makreck/Rase/images/probe/Type_B/Handheld_measuring_probe_08.png

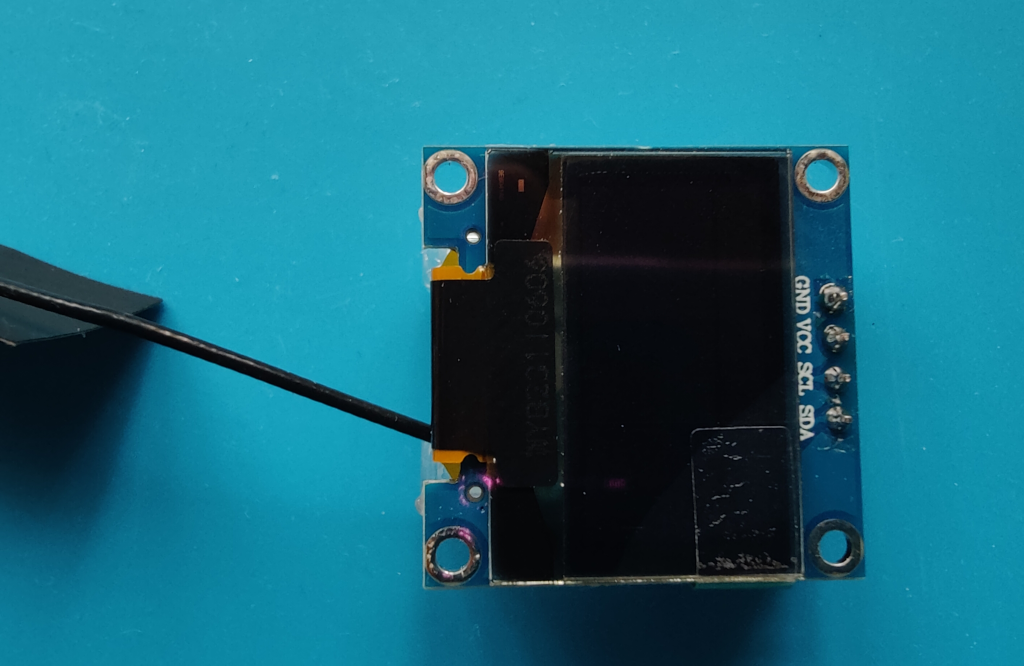
images/probe/Type_B/Handheld_measuring_probe_08.png
