makreck/Rase/images/probe/Type_B/Handheld_measuring_probe_10.png

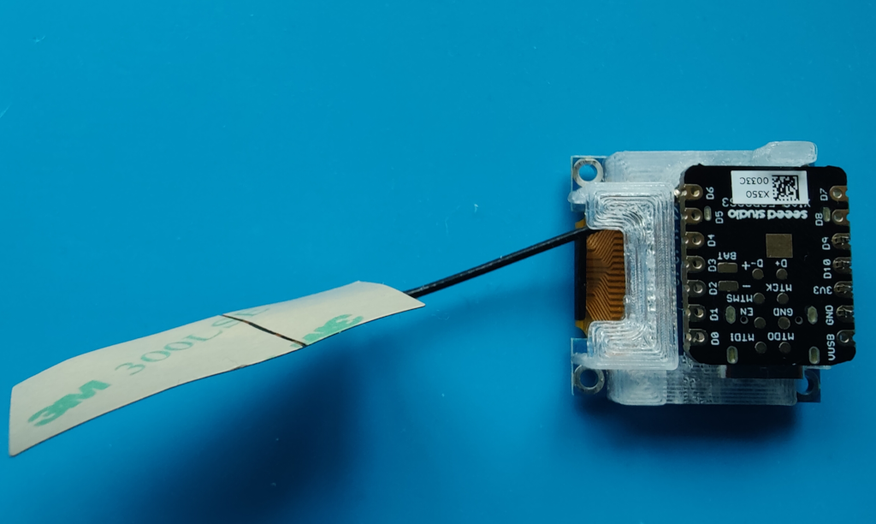
images/probe/Type_B/Handheld_measuring_probe_10.png
