makreck/Rase/images/probe/Type_B/Handheld_measuring_probe_11.png

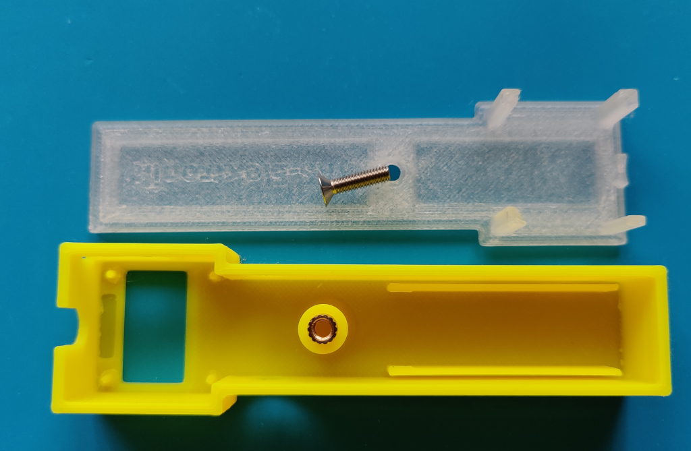
images/probe/Type_B/Handheld_measuring_probe_11.png
