makreck/Rase/images/probe/Type_C/Battless_Rev_C_Menue.jpg

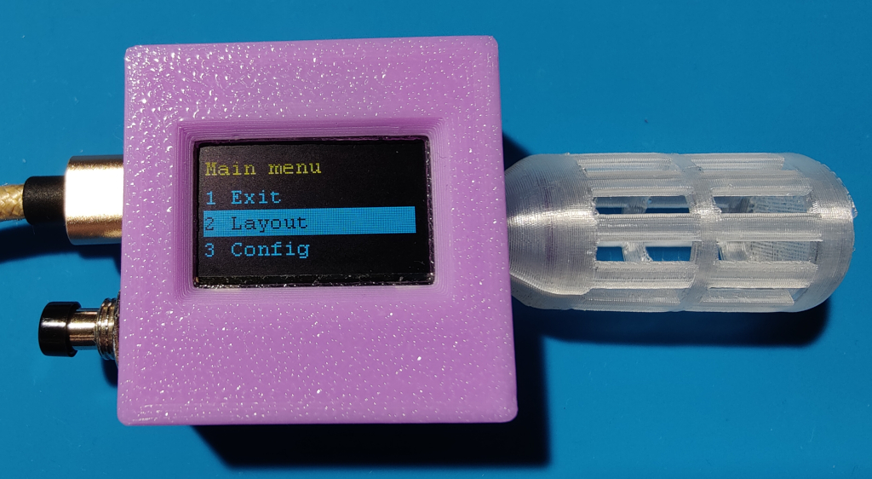
images/probe/Type_C/Battless_Rev_C_Menue.jpg
