makreck/Rase/images/probe/Type_C/Battless_Rev_C_Waveshare_ESP32S3_mini.jpg

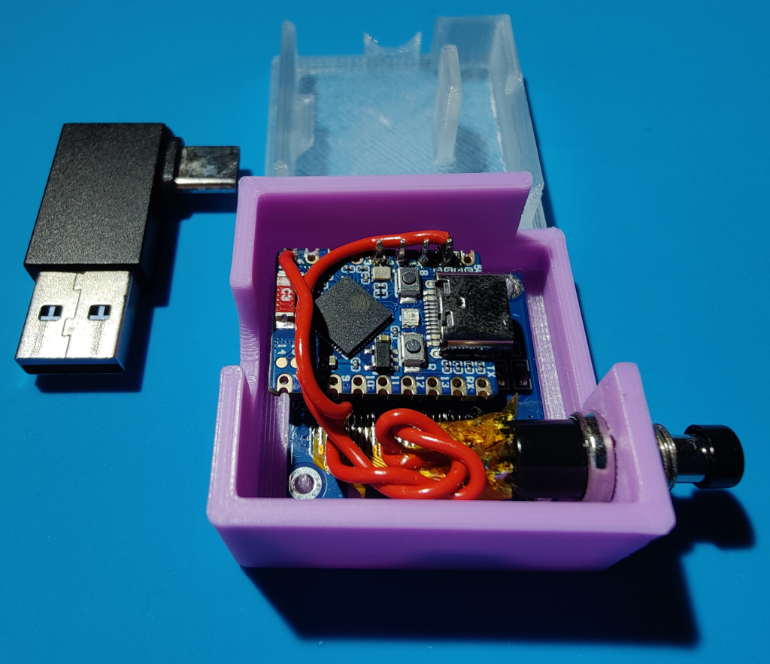
images/probe/Type_C/Battless_Rev_C_Waveshare_ESP32S3_mini.jpg
