makreck/Rase/images/probe/Type_C/Board_Size_ESP32-S3_Super_Mini.jpg

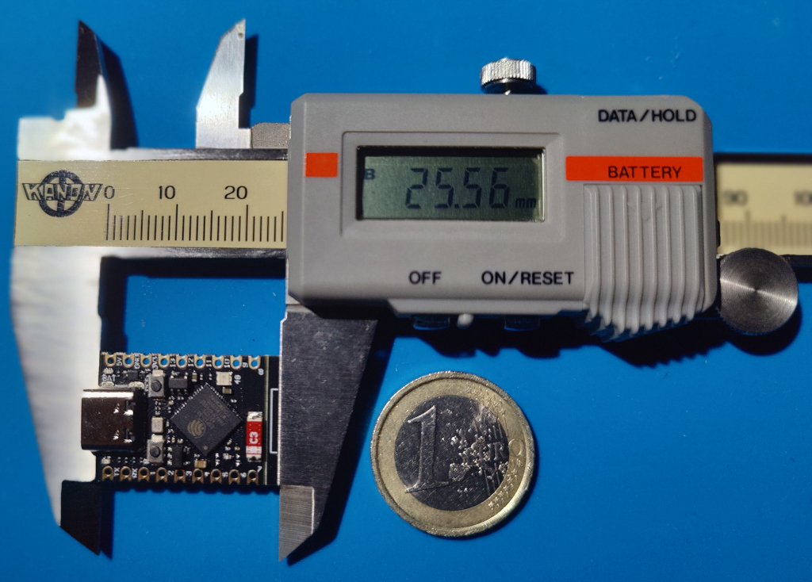
images/probe/Type_C/Board_Size_ESP32-S3_Super_Mini.jpg
