makreck/Rase/images/probe/Type_C/Board_Size_XIAO_ESP32-S3.jpg

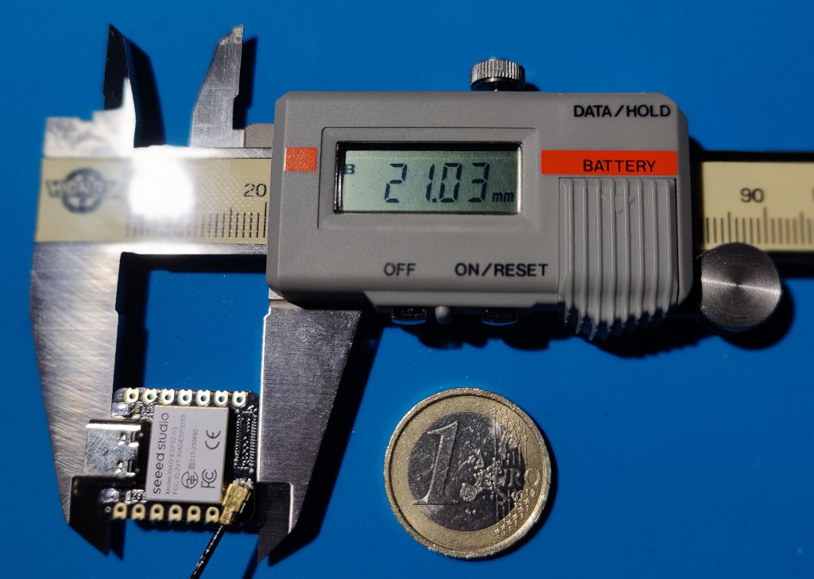
images/probe/Type_C/Board_Size_XIAO_ESP32-S3.jpg
