makreck/Rase/images/probe/Type_C/Board_Type_Sizes.jpg

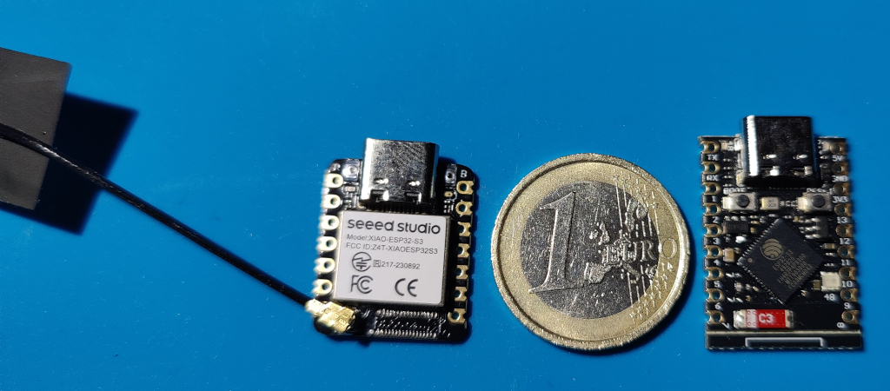
images/probe/Type_C/Board_Type_Sizes.jpg
