makreck/Rase/images/probe/Type_C/Board_Types_Front.jpg

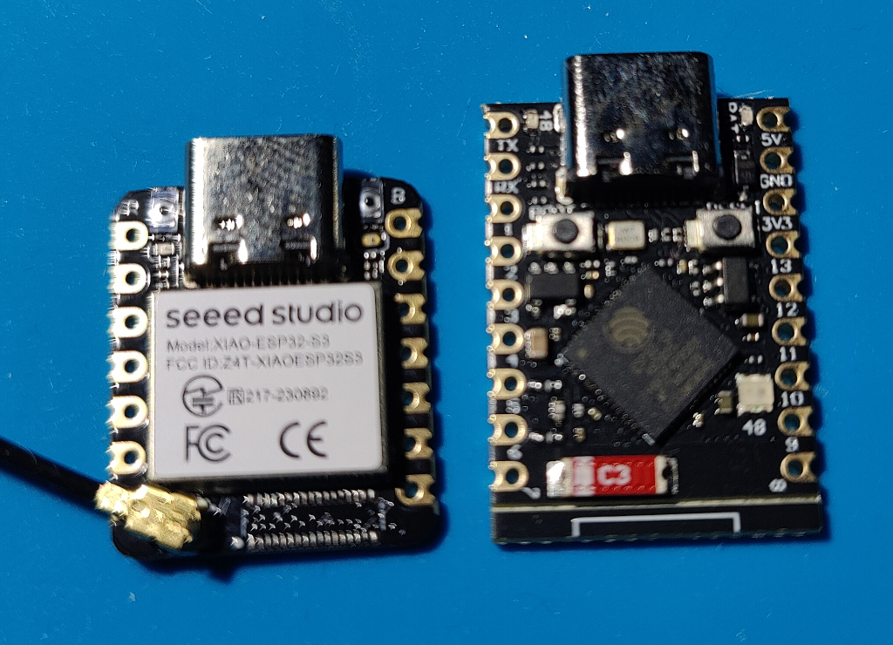
images/probe/Type_C/Board_Types_Front.jpg
