makreck/Rase/images/probe/Type_C/Board_Types_Rear.jpg

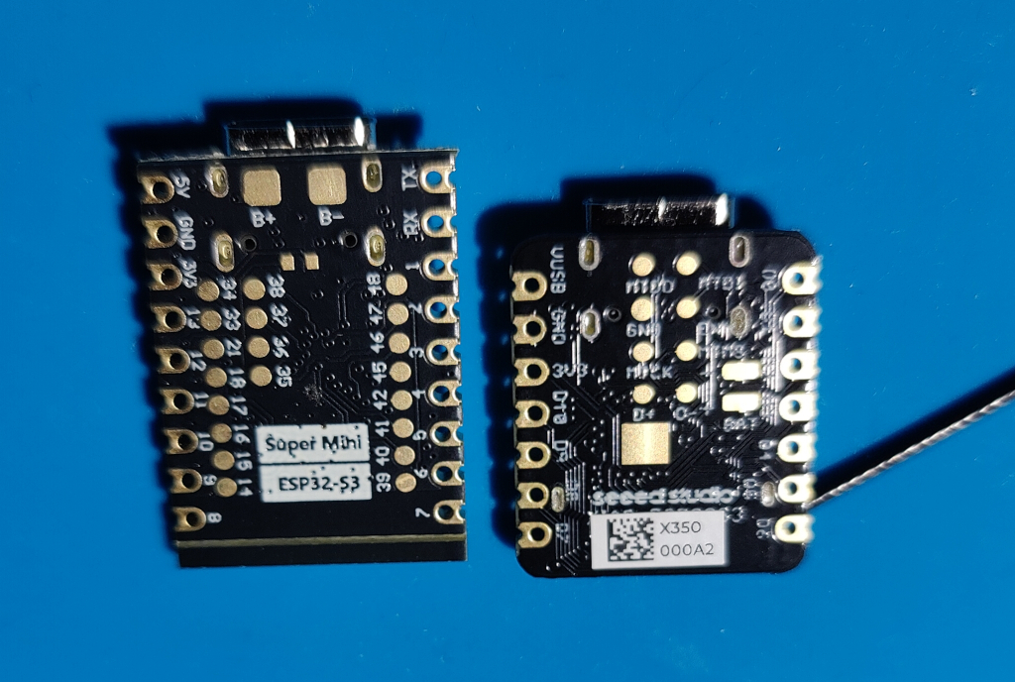
images/probe/Type_C/Board_Types_Rear.jpg
