makreck/Rase/images/probe/Type_C/Housing_Rec_C_M4_Press-Fit-Nut_B.jpg

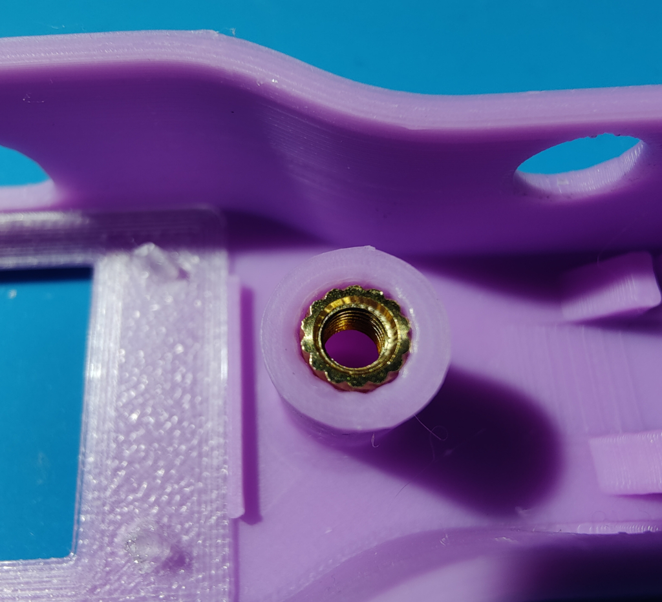
images/probe/Type_C/Housing_Rec_C_M4_Press-Fit-Nut_B.jpg
