makreck/Rase/images/probe/Type_C/Housing_Rec_C_M4_Screw.jpg

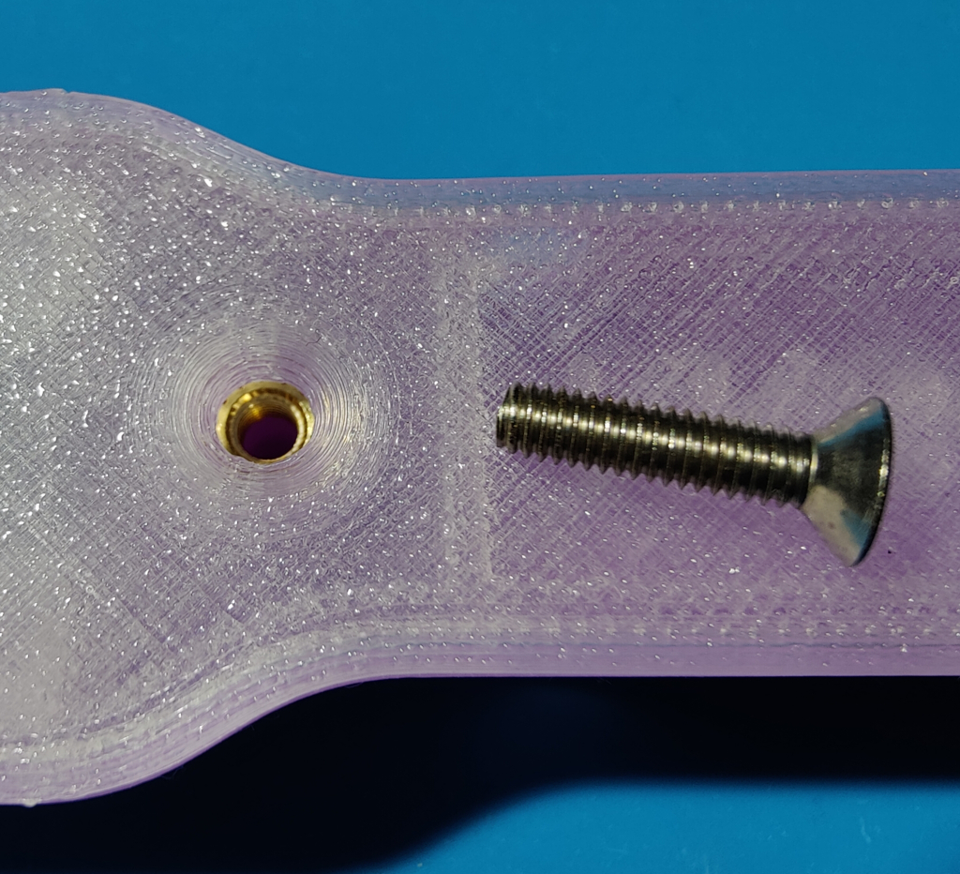
images/probe/Type_C/Housing_Rec_C_M4_Screw.jpg
