makreck/Rase/images/probe/Type_C/Housing_Rec_C_Press-Fit-Nut_A.jpg

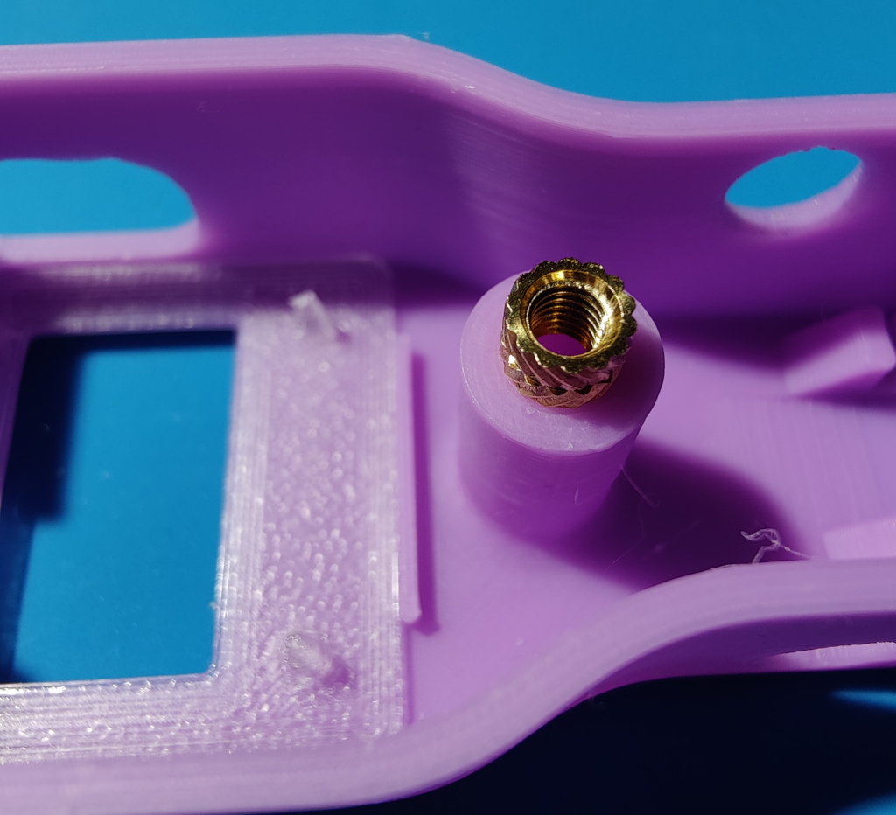
images/probe/Type_C/Housing_Rec_C_Press-Fit-Nut_A.jpg
