makreck/Rase/images/probe/Type_C/Housings_Rev_C.jpg

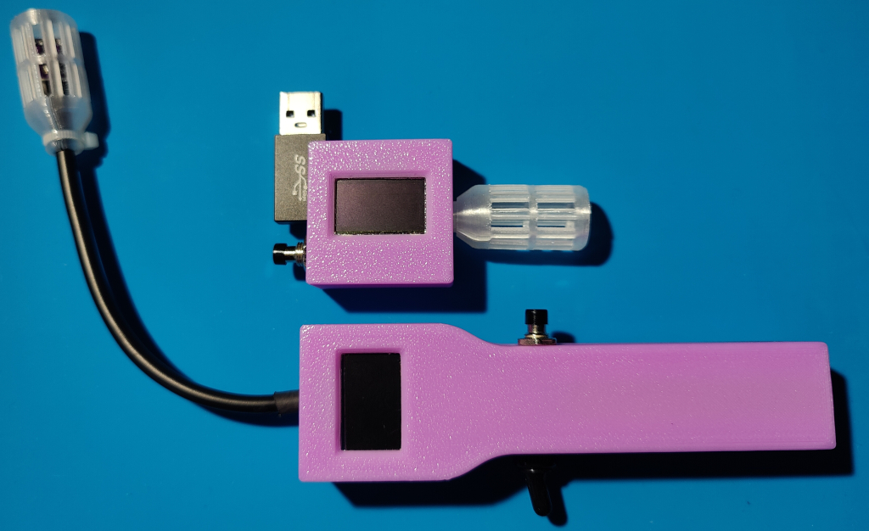
images/probe/Type_C/Housings_Rev_C.jpg
