makreck/Rase/images/probe/Type_C/Insert_Display_Shield.jpg

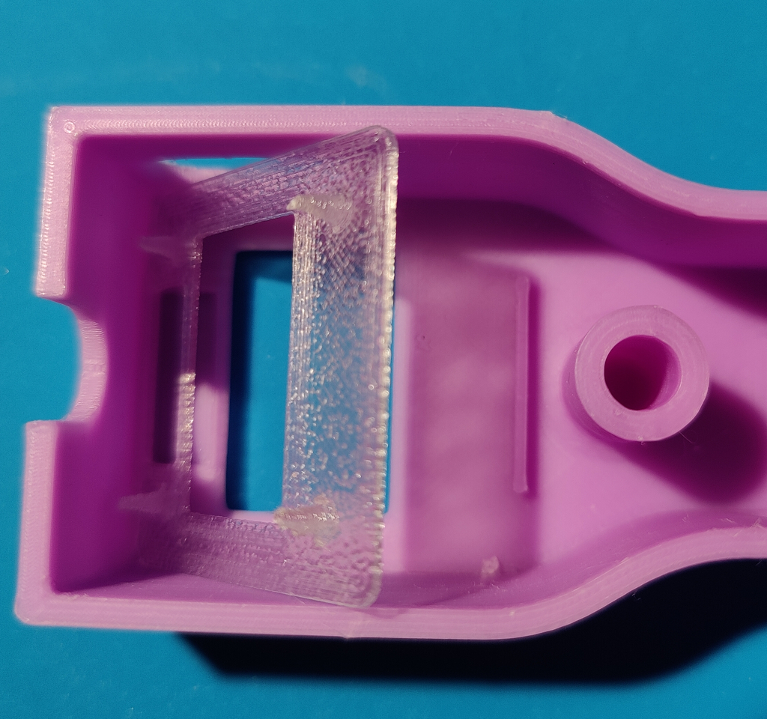
images/probe/Type_C/Insert_Display_Shield.jpg
