makreck/Rase/images/probe/Type_C/Inserted_Display_Shield.jpg

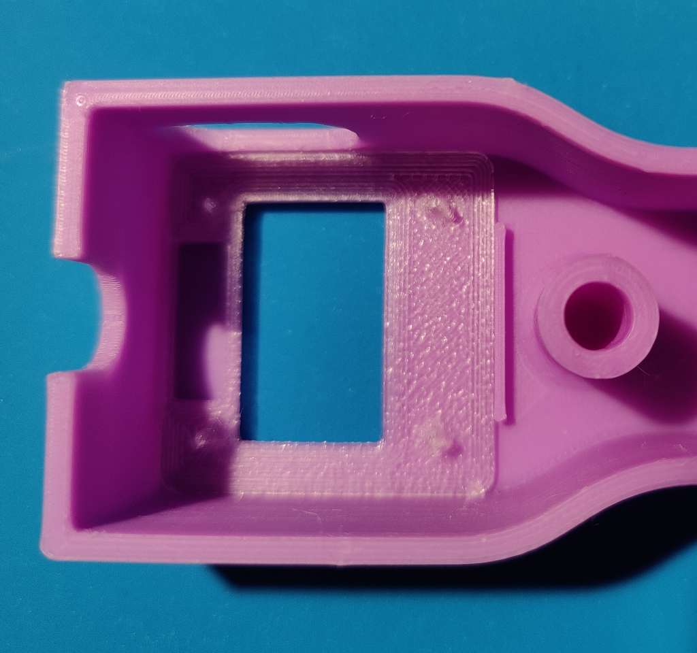
images/probe/Type_C/Inserted_Display_Shield.jpg
