makreck/Rase/images/probe/Type_C/OLED_096_12864_Display_on_Shield.jpg

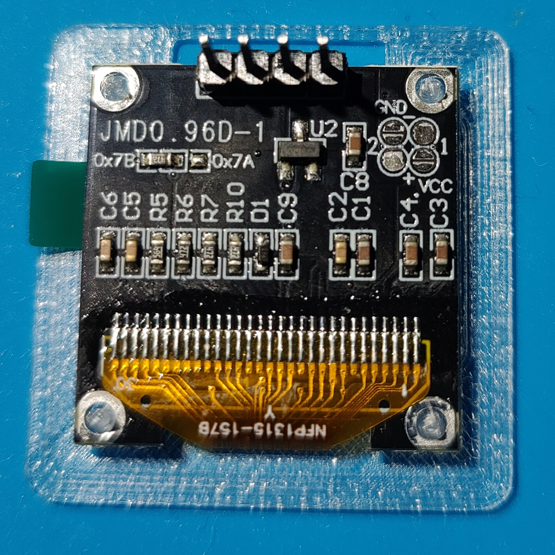
images/probe/Type_C/OLED_096_12864_Display_on_Shield.jpg
