makreck/Rase/images/probe/Type_C/OLED_096_12864_Display_Type_A.jpg

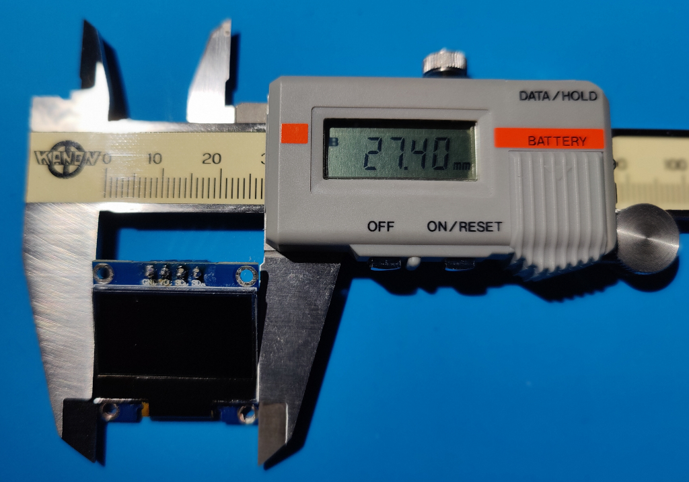
images/probe/Type_C/OLED_096_12864_Display_Type_A.jpg
