makreck/Rase/images/probe/Type_C/OLED_096_12864_Display_Types.jpg

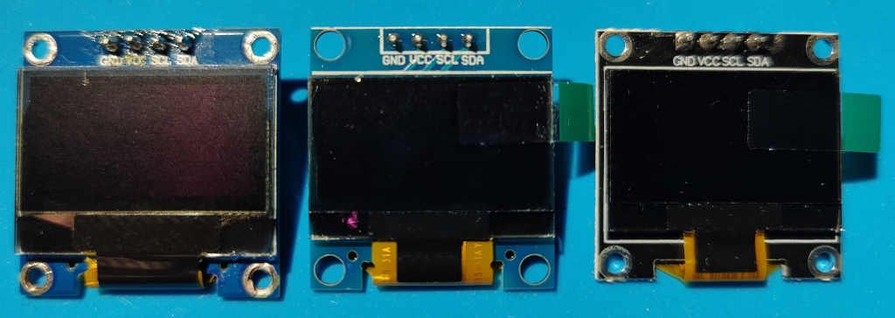
images/probe/Type_C/OLED_096_12864_Display_Types.jpg
