makreck/Rase/images/probe/Type_C/OLED_096_12864_Display_Types_B.jpg

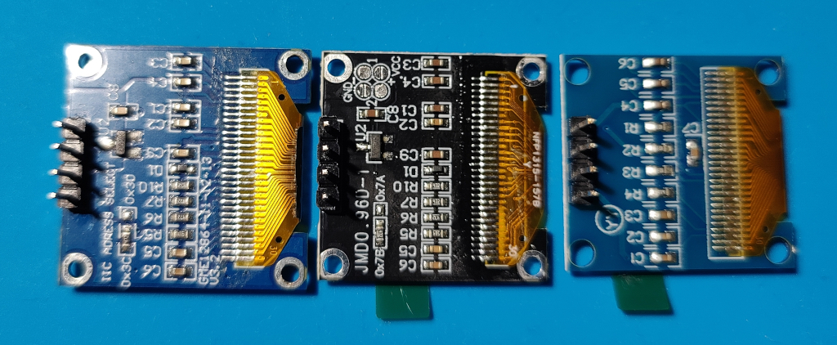
images/probe/Type_C/OLED_096_12864_Display_Types_B.jpg
