makreck/Rase/images/probe/Type_C/Rev_C_complete_open.jpg

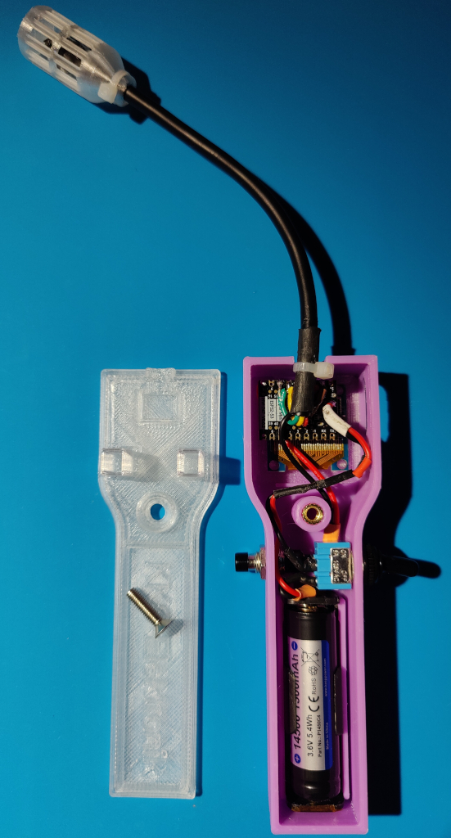
images/probe/Type_C/Rev_C_complete_open.jpg
