makreck/Rase/images/probe/Type_C/Sensor_Protector.jpg

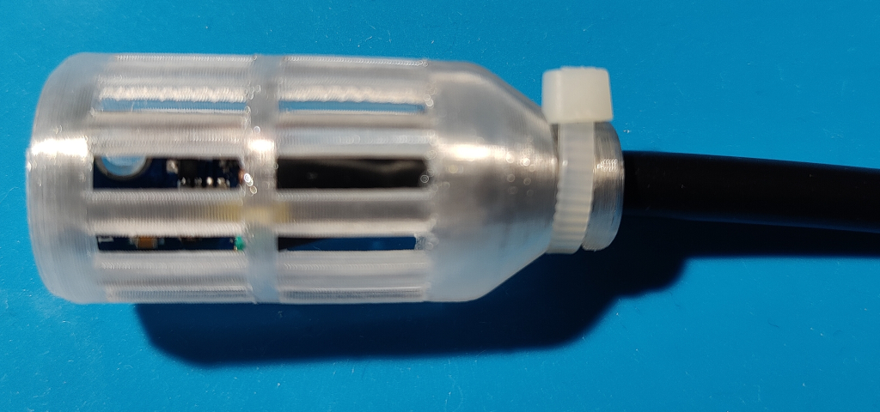
images/probe/Type_C/Sensor_Protector.jpg
