makreck/Rase/images/tool/RASE-Config-Tool.png

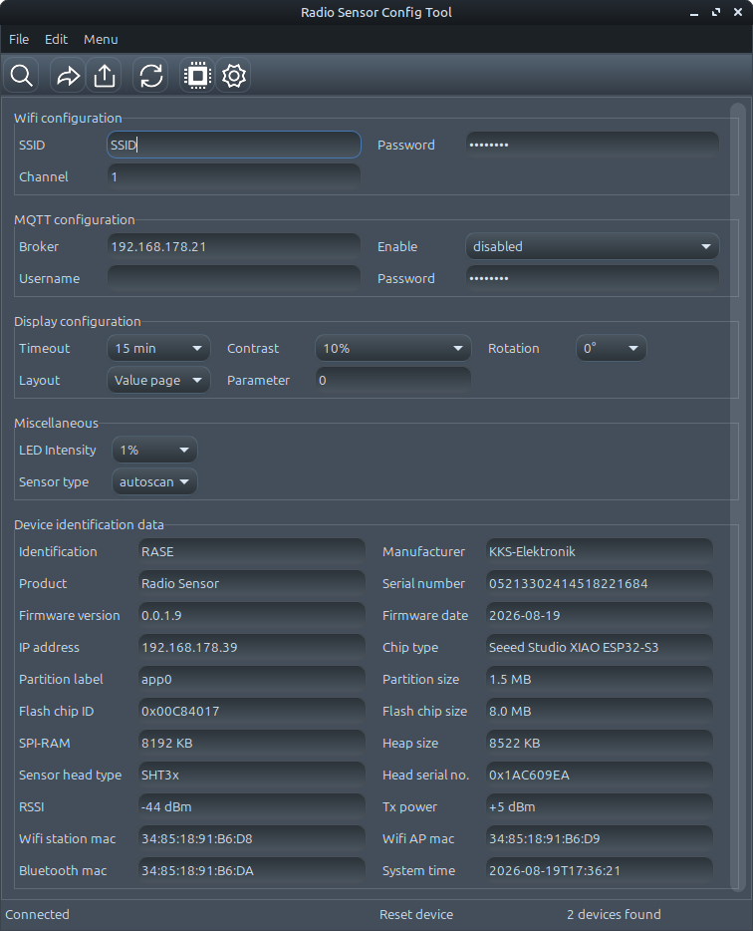
images/tool/RASE-Config-Tool.png
