makreck/Rase/images/web-interface/RASE-Root-Website.png

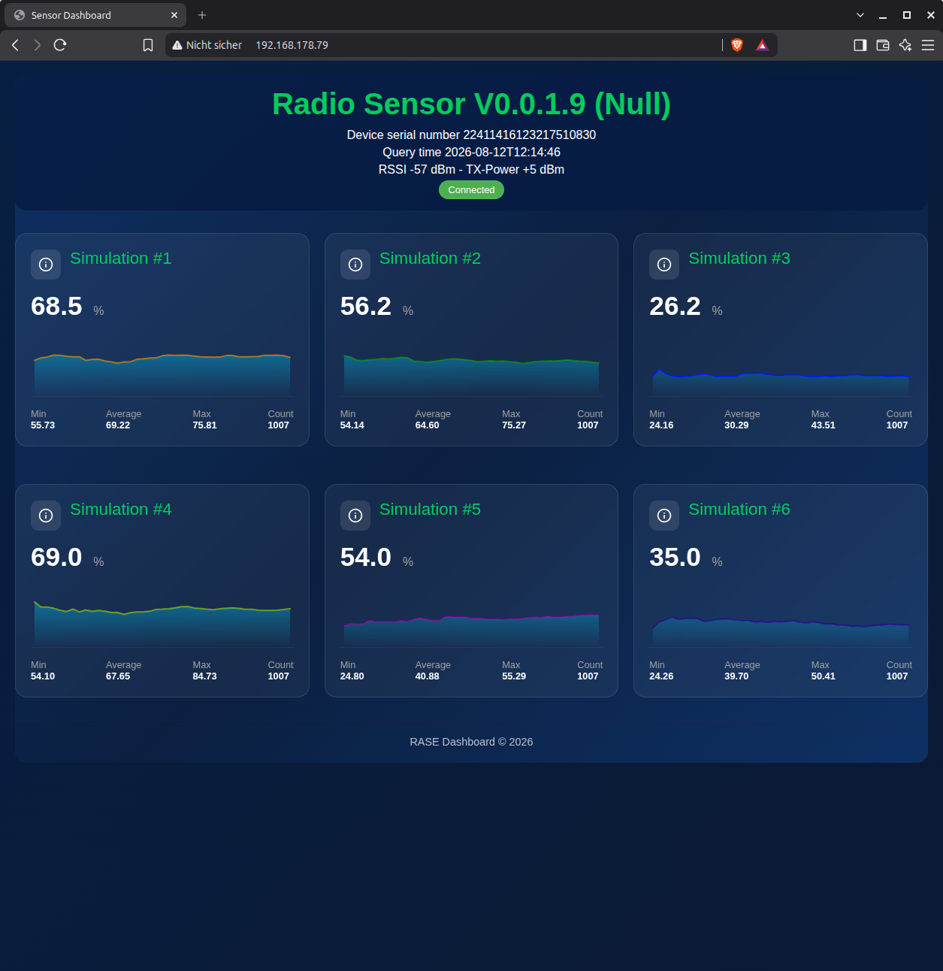
images/web-interface/RASE-Root-Website.png
