makreck/Rase/mechanical/housing/Rev_B/STL/SeeedStudio_XIAO_ESP32S3_Housing_Body.stl

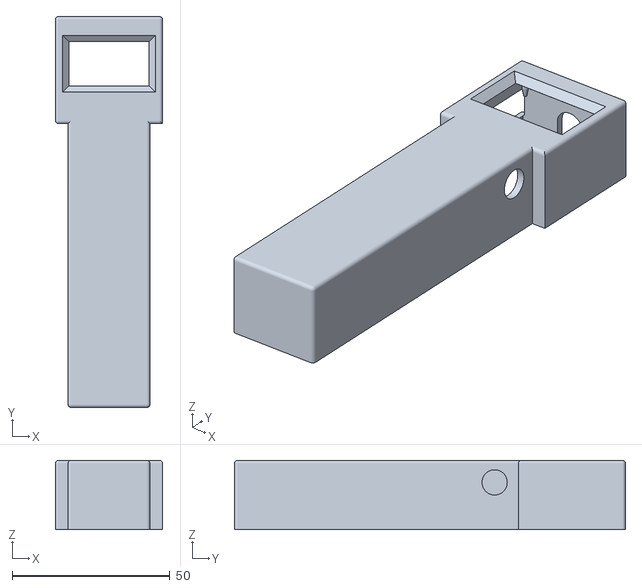
[picture p56: CAD file, 2026-06-11, an earlier design]
mechanical/housing/Rev_B/STL/SeeedStudio_XIAO_ESP32S3_Housing_Body.stl
34.0 x 124.0 x 22.0
