makreck/Rase/images/calibration/Deliquescence_humidity_container_1.png

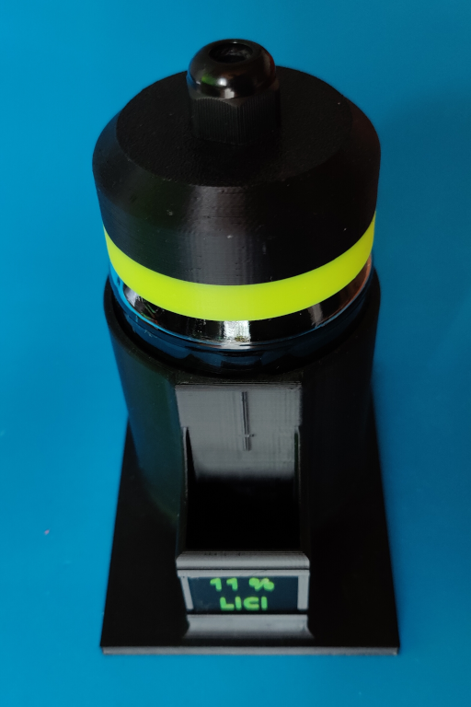
images/calibration/Deliquescence_humidity_container_1.png
