makreck/Rase/images/calibration/Deliquescence_humidity_container_2.png

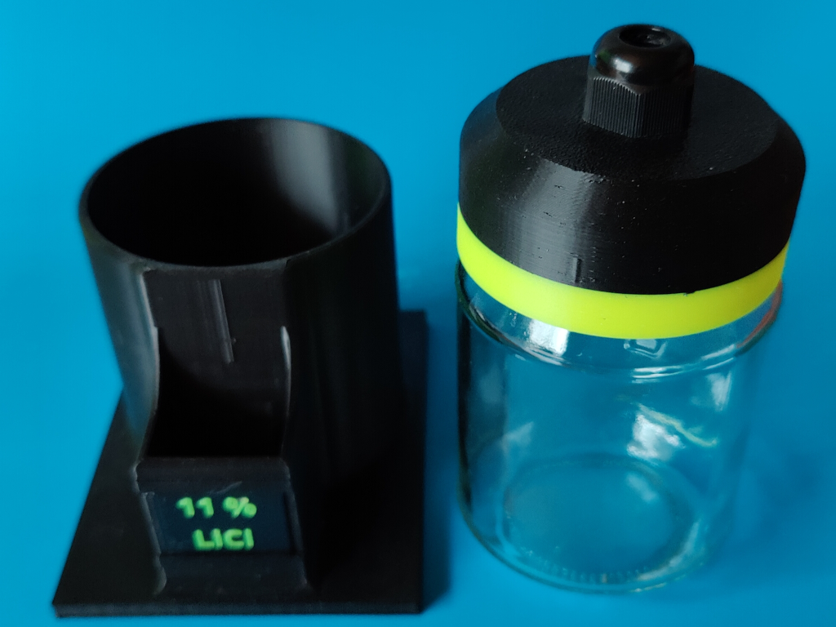
images/calibration/Deliquescence_humidity_container_2.png
