makreck/Rase/images/calibration/Deliquescence_humidity_container_CaCl2_2.png

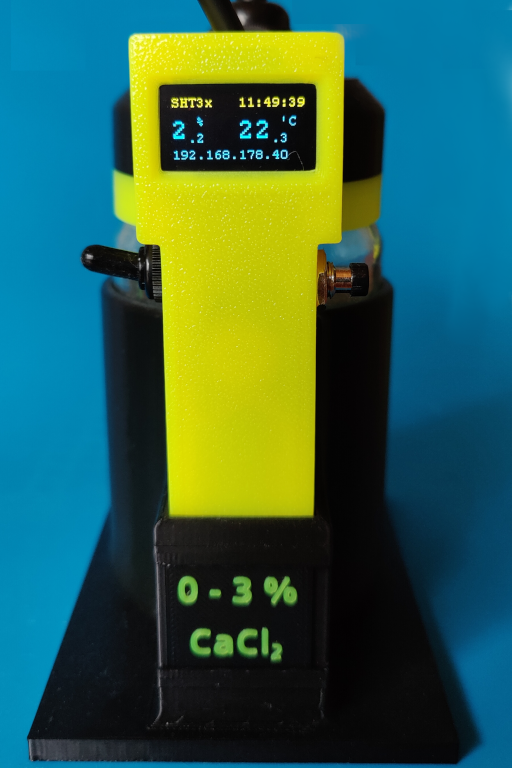
images/calibration/Deliquescence_humidity_container_CaCl2_2.png
