makreck/Rase/images/calibration/Deliquescence_humidity_container_glas.png

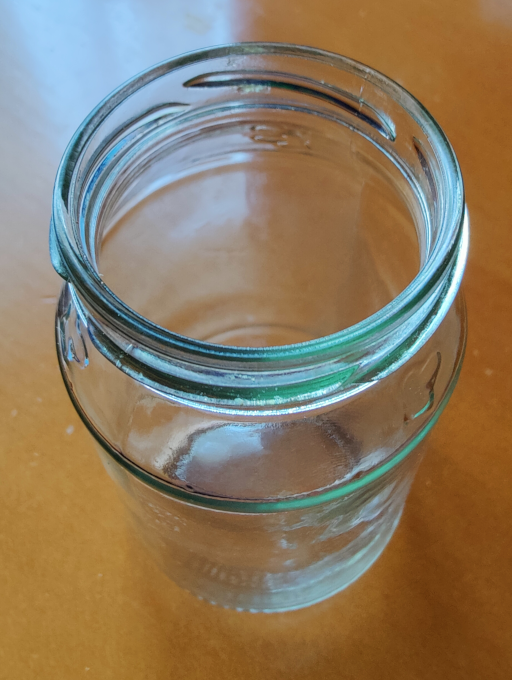
images/calibration/Deliquescence_humidity_container_glas.png
