makreck/Rase/images/calibration/Deliquescence_humidity_container_H2O_100.png

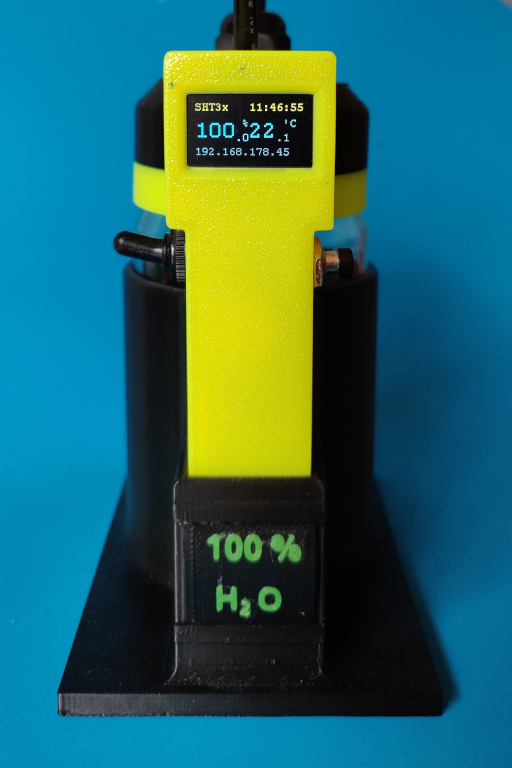
images/calibration/Deliquescence_humidity_container_H2O_100.png
