makreck/Rase/images/calibration/Deliquescence_humidity_container_head.png

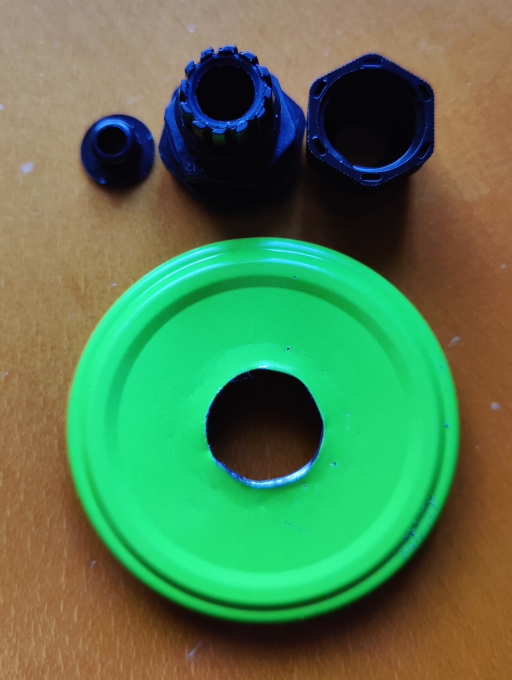
images/calibration/Deliquescence_humidity_container_head.png
