makreck/Rase/images/calibration/Deliquescence_humidity_container_K2Co3_43.png

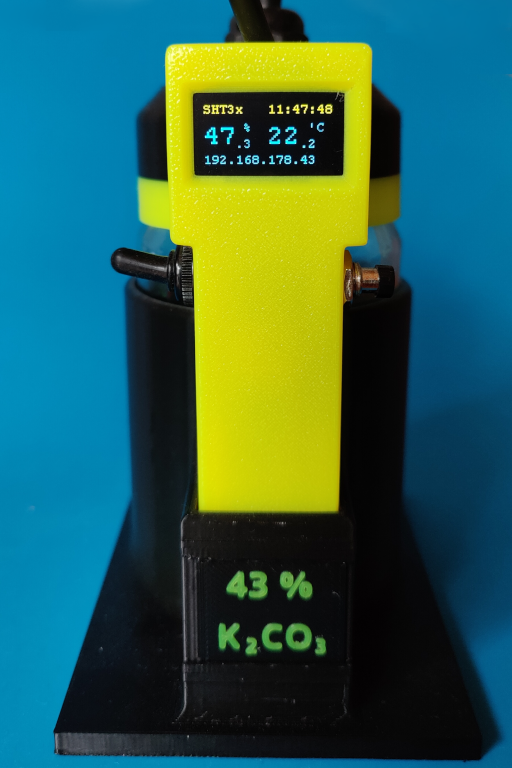
images/calibration/Deliquescence_humidity_container_K2Co3_43.png
