makreck/Rase/images/calibration/Deliquescence_humidity_container_MgCl2_34.png

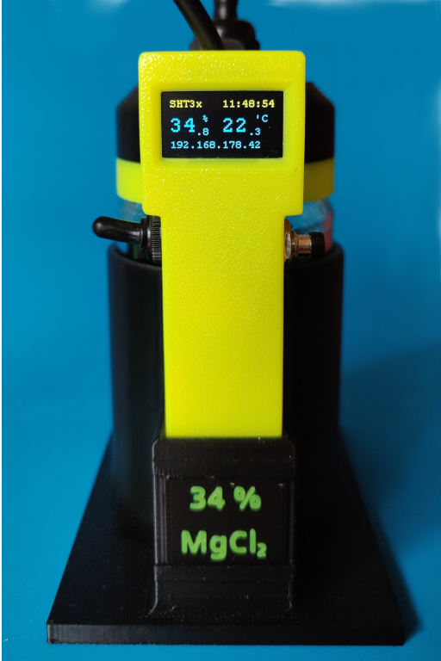
images/calibration/Deliquescence_humidity_container_MgCl2_34.png
