makreck/Rase/firmware/esp32/src/website_config.cpp

/*
 * ==============================================================================
 *
 *  PROJECT:     "Rase" Radio Sensor Project,    ESP32-S3 Station Device Firmware
 *  COPYRIGHT:   (C)2025-2026 KKS-Elektronik,  M. Kreck, <makreck@googlemail.com>
 *
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
 * ==============================================================================
 */

#include "includes.hpp"
#include "app.hpp"

const char *WebServer::config_website_resp_str = R"(
<!DOCTYPE html>
<html lang="en">
<head>
    <meta charset="UTF-8">
    <meta name="viewport" content="width=device-width, initial-scale=1.0">
    <title>Rase Configuration Manager</title>
    <style>
        :root {
            --bg-gradient-0: #01050a;
            --bg-gradient-1: #0b1e42;
            --bg-gradient-2: #0c1830;
            --bg-gradient-3: #071f42;
            --bar-gradient-0: #00b09b;
            --bar-gradient-1: #96c93d;
            --btn-gradient-0: #00805e;
            --btn-gradient-1: #006080;
            --btn-text: #ffffff;
            --btn-text-disabled: #313131;
            --card-bg: rgba(255, 255, 255, 0.05);
            --card-border: rgba(255, 255, 255, 0.1);
            --text-primary: #ffffff;
            --text-secondary: #a0a0a0;
            --text-card-title: #02cc5d;
            --accent-color: #00d2ff;
            --text-shadow: rgba(0, 0, 0, 0.3);
            --box_shadow: rgba(0, 0, 0, 0.5);
            --font-arial: 'Segoe UI', Roboto, Helvetica, Arial, sans-serif;
            --font-mono-1: 'Courier New', Courier, monospace;
            --font-serif-1: 'Segoe UI', Tahoma, Geneva, Verdana, sans-serif;
        }

        * {
            box-sizing: border-box;
            margin: 0;
            padding: 0;
            font-family: var(--font-serif-1);
        }

        body {
            font-family: var(--font-arial);
            color: var(--text-primary);
            min-height: 100vh;
            overflow-x: hidden;
            background: linear-gradient(-45deg, var(--bg-gradient-0), var(--bg-gradient-1), var(--bg-gradient-2), var(--bg-gradient-3));
            background-size: 400% 400%;
            padding: 20px;
        }

        .container {
            max-width: 2400px;
            margin: 0 auto;
            background: linear-gradient(135deg, #0e3063, #0b2041, #0e3063);
            border-radius: 15px;
            box-shadow: 0 10px 30px var(--box-shadow);
            overflow: hidden;
        }

        header {
            text-align: center;
            margin-bottom: 30px;
            padding: 15px;
            background: rgba(5, 26, 66, 0.8);
            border-radius: 15px;
            box-shadow: 0 8px 32px var(--box-shadow);
        }

        h1 {
            font-size: 2.5rem;
            margin-bottom: 10px;
            color: var(--text-card-title);
            text-shadow: 0 2px 10px var(--box-shadow);
        }

        .subtitle {
            font-size: 1.1rem;
            opacity: 0.9;
        }

        label {
            display: block;
            margin-bottom: 5px;
            font-weight: 500;
        }

        .card {
            background: var(--card-bg);
            backdrop-filter: blur(8px);
            -webkit-backdrop-filter: blur(8px);
            border: 1px solid var(--card-border);
            border-radius: 16px;
            padding: 20px;
            margin-bottom: 30px;
            transition: transform 0.3s ease, box-shadow 0.3s ease;
            position: relative;
            overflow: hidden;
            display: flex;
            flex-direction: column;
        }

        .card-title {
            font-size: 1.4rem;
            font-weight: 500;
            margin-bottom: 15px;
            display: flex;
            gap: 10px;
            color: var(--text-card-title);
            align-items: center;
        }

        .card-title i {
            font-size: 1.8rem;
        }

        .card:hover {
            transform: translateY(-5px);
            box-shadow: 0 10px 30px var(--box-shadow);
            border-color: rgba(255, 255, 255, 0.2);
        }

        .card-header {
            display: flex;
            align-items: center;
            margin-bottom: 15px;
        }

        .card-value {
            font-family: var(--font-mono);
            font-size: 2.2rem;
            font-weight: 700;
            margin-bottom: 5px;
            color: var(--text-primary);
        }

        .card-unit {
            font-size: 1rem;
            color: var(--text-secondary);
            font-weight: 500;
            margin-left: 5px;
        }

        .card-stats {
            display: flex;
            justify-content: space-between;
            margin-top: auto;
            padding-top: 15px;
            border-top: 1px solid rgba(255, 255, 255, 0.05);
            font-size: 0.8rem;
            color: var(--text-secondary);
        }

        .icon-box {
            width: 40px;
            height: 40px;
            display: flex;
            align-items: center;
            justify-content: center;
            background: rgba(255, 255, 255, 0.1);
            border-radius: 10px;
            margin-right: 12px;
        }

        .btn-container {
            display: flex;
            justify-content: center;
            gap: 5px;
            margin-top: 10px;
            flex-wrap: wrap;
        }

        .btn {
            background: linear-gradient(to right, var(--btn-gradient-0), var(--btn-gradient-1));
            color: var(--btn-text);
            border: none;
            padding: 12px 25px;
            font-size: 1.1rem;
            border-radius: 50px;
            cursor: pointer;
            transition: all 0.3s ease;
            display: inline-block;
            margin: 10px 5px;
            box-shadow: 0 4px 15px rgba(0, 0, 0, 0.2);
        }

        .btn:hover {
            transform: translateY(-3px);
            box-shadow: 0 6px 20px var(--box-shadow);
        }

        .btn:active {
            transform: translateY(1px);
        }

        .btn:disabled {
            background: #555;
            color: var(--btn-text-disabled);
            cursor: not-allowed;
            transform: none;
            box-shadow: none;
        }

        input,
        select {
            width: 100%;
            padding: 12px;
            border-radius: 5px;
            border: none;
            background: rgba(0, 42, 97, 0.25);
            color: rgb(241, 242, 245);
            font-size: 1rem;
        }

        input:focus,
        select:focus {
            outline: 2px solid var(--text-card-title);
            background: rgba(1, 62, 119, 0.9);
        }

        .password-field {
            position: relative;
        }

        .toggle-password {
            position: absolute;
            right: 10px;
            top: 50%;
            transform: translateY(-50%);
            cursor: pointer;
            color: var(--text-card-title);
        }

        .status {
            text-align: center;
            padding: 15px;
            margin-top: 20px;
            border-radius: 5px;
            display: none;
        }

        .progress-container {
            margin-top: 20px;
            display: none;
        }

        .progress-bar {
            height: 10px;
            background: rgba(255, 255, 255, 0.1);
            border-radius: 5px;
            overflow: hidden;
        }

        .progress {
            height: 100%;
            background: linear-gradient(to right, var(--bar-gradient-0), var(--bar-gradient-1));
            width: 0%;
            transition: width 0.4s ease;
        }

        .success {
            background: rgba(6, 214, 160, 0.2);
            border: 1px solid #06d6a0;
            color: #06d6a0;
            display: block;
        }

        .error {
            background: rgba(239, 71, 111, 0.2);
            border: 1px solid #ef476f;
            color: #ef476f;
            display: block;
        }

        .loading {
            display: none;
            text-align: center;
            padding: 20px;
        }

        .spinner {
            border: 4px solid rgba(13, 3, 59, 0.3);
            border-radius: 50%;
            border-top: 4px solid var(--text-card-title);
            width: 30px;
            height: 30px;
            animation: spin 1s linear infinite;
            margin: 0 auto;
        }

        footer {
            text-align: center;
            padding: 20px;
            font-size: 0.9rem;
            opacity: 0.7;
            border-top: 1px solid rgba(182, 6, 6, 0.1);
        }

        @keyframes spin {
            0% {
                transform: rotate(0deg);
            }

            100% {
                transform: rotate(360deg);
            }
        }





        .form-group {
            margin-bottom: 15px;
            padding: 8px;
            background: linear-gradient(0deg, #0e3063, #0b2041, #0e3063);
            color: #a0beff;
        }

        .config-container {
            padding: 30px;
        }

        @media (max-width: 768px) {
            .container {
                margin: 10px;
            }

            .config-container {
                padding: 15px;
            }

            h1 {
                font-size: 2rem;
            }

            .btn-container {
                flex-direction: column;
                align-items: center;
            }

            .btn {
                width: 80%;
            }
        }
    </style>
</head>

<body>
    <div class="container">
        <header>
            <h1>RASE Configuration Manager</h1>
            <p class="subtitle">Manage device settings and save changes to the server</p>
        </header>

        <div class="config-container">
            <div class="card">
                <h2 class="card-title">WiFi Settings</h2>
                <div class="form-group">
                    <label for="ssid">SSID</label>
                    <input type="text" id="ssid" name="ssid">
                </div>
                <div class="form-group">
                    <label for="password">Password</label>
                    <div class="password-field">
                        <input type="password" id="password" name="password">
                        <span class="toggle-password" id="toggle-password">👁️</span>
                    </div>
                </div>
                <div class="form-group">
                    <label for="wifi_channel">WiFi Channel</label>
                    <!-- <input type="text" id="wifi_channel" name="wifi_channel"> -->
                    <select id="wifi_channel" name="wifi_channel">
                        <option value="1">Channel 1</option>
                        <option value="2">Channel 2</option>
                        <option value="3">Channel 3</option>
                        <option value="4">Channel 4</option>
                        <option value="5">Channel 5</option>
                        <option value="6">Channel 6</option>
                        <option value="7">Channel 7</option>
                        <option value="8">Channel 8</option>
                        <option value="9">Channel 9</option>
                        <option value="10">Channel 10</option>
                        <option value="11">Channel 11</option>
                    </select>
                </div>
            </div>

            <div class="card">
                <h2 class="card-title">MQTT Settings</h2>
                <div class="form-group">
                    <label for="mqtt_broker">MQTT Broker IP</label>
                    <input type="text" id="mqtt_broker" name="mqtt_broker">
                </div>
                <div class="form-group">
                    <label for="mqtt_username">MQTT Username</label>
                    <input type="text" id="mqtt_username" name="mqtt_username">
                </div>
                <div class="form-group">
                    <label for="mqtt_password">MQTT Password</label>
                    <div class="password-field">
                        <input type="password" id="mqtt_password" name="mqtt_password">
                        <span class="toggle-password" id="toggle-mqtt-password">👁️</span>
                    </div>
                </div>
                <div class="form-group">
                    <label for="mqtt_enable">MQTT Enable</label>
                    <select id="mqtt_enable" name="mqtt_enable">
                        <option value="enabled">Enabled</option>
                        <option value="disabled">Disabled</option>
                    </select>
                </div>
            </div>

            <div class="card">
                <h2 class="card-title">Display Settings</h2>
                <div class="form-group">
                    <label for="display_layout">Display Layout</label>
                    <select id="display_layout" name="display_layout">
                        <option value="Value page">Value page</option>
                        <option value="Details page">Details page</option>
                        <option value="Info page">Info page</option>
                    </select>
                </div>
                <div class="form-group">
                    <label for="display_param">Display Parameter (0-255)</label>
                    <input type="number" id="display_param" name="display_param" min="0" max="255" value="0">
                </div>
                <div class="form-group">
                    <label for="display_rotation">Display Rotation</label>
                    <select id="display_rotation" name="display_rotation">
                        <option value="0°">0°</option>
                        <option value="180°">180°</option>
                    </select>
                </div>
                <div class="form-group">
                    <label for="display_timeout">Display Timeout</label>
                    <select id="display_timeout" name="display_timeout">
                        <option value="Never">Never</option>
                        <option value="10 s">10 s</option>
                        <option value="1 min">1 min</option>
                        <option value="5 min">5 min</option>
                        <option value="15 min">15 min</option>
                        <option value="30 min">30 min</option>
                    </select>
                </div>
                <div class="form-group">
                    <label for="display_contrast">Display Contrast</label>
                    <select id="display_contrast" name="display_contrast">
                        <option value="100%">100%</option>
                        <option value="80%">80%</option>
                        <option value="60%">60%</option>
                        <option value="50%">50%</option>
                        <option value="40%">40%</option>
                        <option value="30%">30%</option>
                        <option value="20%">20%</option>
                        <option value="10%">10%</option>
                    </select>
                </div>
            </div>

            <div class="card">
                <h2 class="card-title">Sensor Settings</h2>
                <div class="form-group">
                    <label for="sensor_type">Sensor Type</label>
                    <select id="sensor_type" name="sensor_type">
                        <option value="autoscan">autoscan</option>
                        <option value="Null">Null</option>
                        <option value="SHT2x">SHT2x</option>
                        <option value="SHT3x">SHT3x</option>
                        <option value="HTU21d">HTU21d</option>
                        <option value="ATHxx">ATHxx</option>
                        <option value="HDC1080">HDC1080</option>
                        <option value="BMx280">BMx280</option>
                    </select>
                </div>
            </div>

            <div class="card">
                <h2 class="card-title">LED Settings</h2>
                <div class="form-group">
                    <label for="led_intensity">LED Intensity</label>
                    <select id="led_intensity" name="led_intensity">
                        <option value="100%">100%</option>
                        <option value="75%">75%</option>
                        <option value="50%">50%</option>
                        <option value="25%">25%</option>
                        <option value="10%">10%</option>
                        <option value="1%">1%</option>
                    </select>
                </div>
                <div class="form-group">
                    <label for="led_color_order">LED Color Order</label>
                    <select id="led_color_order" name="led_color_order">
                        <option value="RGB">R - G - B</option>
                        <option value="BRG">B - R - G</option>
                        <option value="BGR">B - G - R</option>
                    </select>
                </div>
            </div>

            <div class="btn-container">
                <button class="btn" id="load-btn">Load Configuration</button>
                <button class="btn" id="save-btn">Save Configuration</button>
            </div>

            <div class="loading" id="loading">
                <div class="spinner"></div>
                <p>Processing request...</p>
            </div>

            <div class="status" id="status"></div>
        </div>

        <footer>
            <p>RASE Configuration Manager &copy; 2026</p>
        </footer>
    </div>

    <script>
        document.addEventListener('DOMContentLoaded', function () {
            const togglePassword = document.getElementById('toggle-password');
            const passwordInput = document.getElementById('password');

            const toggleMqttPassword = document.getElementById('toggle-mqtt-password');
            const mqttPasswordInput = document.getElementById('mqtt_password');

            togglePassword.addEventListener('click', function () {
                const type = passwordInput.getAttribute('type') === 'password' ? 'text' : 'password';
                passwordInput.setAttribute('type', type);
                this.textContent = type === 'password' ? '👁️' : '🔒';
            });

            toggleMqttPassword.addEventListener('click', function () {
                const type = mqttPasswordInput.getAttribute('type') === 'password' ? 'text' : 'password';
                mqttPasswordInput.setAttribute('type', type);
                this.textContent = type === 'password' ? '👁️' : '🔒';
            });

            document.getElementById('load-btn').addEventListener('click', loadConfiguration);
            document.getElementById('save-btn').addEventListener('click', saveConfiguration);

            loadConfiguration();

            function loadConfiguration() {
                showLoading(true);
                const status = document.getElementById('status');

                setTimeout(() => {
                    try {
                        fetch('/api/config')
                            .then(response => response.json())
                            .then(data => populateForm(data))

                        status.textContent = 'Configuration loaded successfully!';
                        status.style.backgroundColor = '#4CAF50';
                        status.style.display = 'block';
                    } catch (error) {
                        status.textContent = 'Error loading configuration: ' + error.message;
                        status.style.backgroundColor = '#f44336';
                        status.style.display = 'block';
                    }

                    showLoading(false);
                }, 1000);
            }

            function saveConfiguration() {
                showLoading(true);
                const status = document.getElementById('status');

                const formData = {};
                const inputs = document.querySelectorAll('input, select');

                inputs.forEach(input => {
                    if (input.name) {
                        if (input.type === 'checkbox') {
                            formData[input.name] = input.checked;
                        } else {
                            formData[input.name] = input.value;
                        }
                    }
                });

                setTimeout(() => {
                    try {
                        fetch('/api/config', {
                            method: 'PUT',
                            headers: {
                                'Content-Type': 'application/json'
                            },
                            body: JSON.stringify(formData)
                        })
                        .then(response => response.json())
                        .then(data => {
                            status.textContent = 'Configuration saved successfully!';
                            status.style.backgroundColor = '#4CAF50';
                            status.style.display = 'block';
                        });

                        status.textContent = 'Configuration saved successfully!';
                        status.style.backgroundColor = '#4CAF50';
                        status.style.display = 'block';
                    } catch (error) {
                        status.textContent = 'Error saving configuration: ' + error.message;
                        status.style.backgroundColor = '#f44336';
                        status.style.display = 'block';
                    }

                    showLoading(false);
                }, 1000);
            }

            function populateForm(data) {
                for (const key in data) {
                    const element = document.getElementById(key);
                    if (element) {
                        if (element.tagName === 'SELECT') {
                            element.value = data[key];
                        } else if (element.type === 'checkbox') {
                            element.checked = data[key];
                        } else {
                            element.value = data[key];
                        }
                    }
                }
            }

            function showLoading(show) {
                const loading = document.getElementById('loading');
                if (show) {
                    loading.style.display = 'block';
                } else {
                    loading.style.display = 'none';
                }
            }
        });
    </script>
</body>
</html>
)";
