makreck/Rase/app/debian/include/widget_sensor.h

/*
 * ==============================================================================
 *
 *  PROJECT:     "Rase" Radio Sensor Project,    Measuring and Config Application
 *  COPYRIGHT:   (C)2025-2026 KKS-Elektronik,  M. Kreck, <makreck@googlemail.com>
 *
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
 * ==============================================================================
 */

#pragma once

#define SENSOR_LIST_ITEM_WIDTH  (128)
#define SENSOR_LIST_ITEM_HEIGHT (128)

class SensorWidget {
    private:
        struct {
            SensorConnection* device         = nullptr;
            SidebarWidget*    sidebar_widget = nullptr;

            RectEx rc_widget;
            
            int  taskbar_indent = 1;
            bool request_redraw = true;

            struct {
                GtkWidget* row;
                GtkWidget* grid;
                GtkWidget* sidebar;
                GtkWidget* image;
                GtkWidget* label;
                GtkWidget* bar;
                GtkWidget* bar_label;
            } gtk;

            union {
                uint8_t data = 0;
                struct {
                    uint8_t fShiftKeyDown : 1;
                    uint8_t fCtrlKeyDown : 1;
                    uint8_t fAltKeyDown : 1;

                    uint8_t fLeftBtnDown : 1;
                    uint8_t fMidBtnDown : 1;
                    uint8_t fRightBtnDown : 1;

                    uint8_t fDoubleClick : 1;
                    uint8_t fTrippleClick : 1;
                } flag;
                struct {
                    uint8_t fAuxKeyDown : 3;
                    uint8_t fBtnDown    : 3;
                    uint8_t fMultiClick : 2;
                } group;
            } event;
            
            float eventTime_s = 0.0f;
            uint32_t eventTimeStamp_ms = 0;
            PointF eventPt;
            PointF currentPt;

        } m;

        void init(SensorConnection* _device, int _side_bar_number = 0);
        void cleanup(void);

        static gboolean _eventHandler_ChannelWidget(GtkWidget* _widget, GdkEvent* _event, gpointer _data);
        static gboolean _eventHandler_SidebarWidget(GtkWidget* _widget, GdkEvent* _event, gpointer _data);

        void eventHandler(int _type, void* _holder, GdkEvent* _event);
        void handleMouseButtonEvent(int type, void* holder, GdkEventButton* btnEvent);
        void handleScrollEvent(GdkEventScroll* _scroll_event);
        void handleEnterLeave(int _type, ChannelWidget* _holder, GdkEventCrossing* _event);
        void handleMouseMoveEvent(int _type, ChannelWidget* _holder, GdkEventMotion* _motion_event);
        void processEventState(guint state);
        bool processEventTime(uint32_t timeValue);
        bool processMouseClicks(int type, void* holder);
        bool processKeyStates(GdkEventButton* btnEvent);
        bool handleButtonRelease(void);
        bool select_channel(ChannelWidget* holder);
        int  create_label(void);
        int  create_sidebar(void);
        int  create_channel_list(void);
        int  update_channel_list(void);

    public:
        SensorWidget(SensorConnection* _device, int _side_bar_number) {
            init(_device, _side_bar_number);
        }
        
        ~SensorWidget() {
            cleanup();
        }

        void set_sidebar_number(int _side_bar_number);
        void select_channels(int index, bool _hilighted, bool _selected, uint8_t _flags = 0x03);

        GtkWidget* get_row()       { return (m.gtk.row);       }
        GtkWidget* get_grid()      { return (m.gtk.grid);      }
        GtkWidget* get_sidebar()   { return (m.gtk.sidebar);   }
        GtkWidget* get_image()     { return (m.gtk.image);     }
        GtkWidget* get_label()     { return (m.gtk.label);     }
        GtkWidget* get_bar()       { return (m.gtk.bar);       }
        GtkWidget* get_bar_label() { return (m.gtk.bar_label); }
};
