makreck/Rase/firmware/esp32/src/config_interface.cpp

/*
 * ==============================================================================
 *
 *  PROJECT:     "Rase" Radio Sensor Project,    ESP32-S3 Station Device Firmware
 *  COPYRIGHT:   (C)2025-2026 KKS-Elektronik,  M. Kreck, <makreck@googlemail.com>
 *
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
 * ==============================================================================
 */

#include "app.hpp"

#define DISPLAY_STATE

void ConfigInterface::init(void) {
    setup();
    xTaskCreate(ConfigInterface::_communication_handler, "ConfigInterface", TASK_DEFAULT_STACKSIZE, this, TASK_DEFAULT_PRIORITY, &task_handle);
}

void ConfigInterface::cleanup(void) {
	if (task_handle != nullptr) {
		vTaskDelete(task_handle);
		task_handle = nullptr;
	}
}

void ConfigInterface::setup(void) {

    // Avoid conflicts with JTAG interface during boot sequence!
#ifdef ENABLE_JTAG_CONFIG_INTERFACE
    usb_serial_jtag_driver_uninstall();
#else
    uart_driver_delete(UART_NUM_0);
#endif
    vTaskDelay(pdMS_TO_TICKS(250));

    uart_config_t uart_config;
    uart_config.baud_rate  = CONFIG_INTERFACE_BAUDRATE;
    uart_config.data_bits  = UART_DATA_8_BITS;
    uart_config.parity     = UART_PARITY_DISABLE;
    uart_config.stop_bits  = UART_STOP_BITS_1;
    uart_config.flow_ctrl  = UART_HW_FLOWCTRL_DISABLE;
    uart_config.source_clk = UART_SCLK_APB;
    uart_param_config(UART_NUM_0, &uart_config);

    uart_set_pin(UART_NUM_0, UART_PIN_NO_CHANGE, UART_PIN_NO_CHANGE, UART_PIN_NO_CHANGE, UART_PIN_NO_CHANGE);

#ifdef ENABLE_JTAG_CONFIG_INTERFACE
    usb_serial_jtag_driver_config_t jtag_cfg;
    jtag_cfg.tx_buffer_size = TX_BUFFER_SIZE;
    jtag_cfg.rx_buffer_size = RX_BUFFER_SIZE;
    usb_serial_jtag_driver_install(&jtag_cfg);
#else
    uart_driver_install(UART_NUM_0, RX_BUFFER_SIZE, TX_BUFFER_SIZE, 0, NULL, 0);
#endif
}

void ConfigInterface::_communication_handler(void *pvParameters) {
    (reinterpret_cast<ConfigInterface*>(pvParameters))->communication_handler();
}
void ConfigInterface::communication_handler(void) {
    while (true) {
#ifdef ENABLE_JTAG_CONFIG_INTERFACE
        int len = 0;
        int bytes_read = usb_serial_jtag_read_bytes(rx_buffer, RX_BUFFER_SIZE, pdMS_TO_TICKS(100));
        while (bytes_read > 0) {
            len += bytes_read;
            bytes_read = usb_serial_jtag_read_bytes(&rx_buffer[len], RX_BUFFER_SIZE - len - 1, pdMS_TO_TICKS(100));
        }
#else
        int len = 0;
        int bytes_read = uart_read_bytes(UART_NUM_0, rx_buffer, RX_BUFFER_SIZE, pdMS_TO_TICKS(100));
        while (bytes_read > 0) {
            len += bytes_read;
            bytes_read = uart_read_bytes(UART_NUM_0, &rx_buffer[len], RX_BUFFER_SIZE - len - 1, pdMS_TO_TICKS(100));
        }
#endif
        if (len > 0) {
            process_command(rx_buffer, (size_t)len);
            memset(rx_buffer, 0, RX_BUFFER_SIZE);
        }

        vTaskDelay(pdMS_TO_TICKS(100));
    }
}

ssize_t ConfigInterface::send(const char* data, size_t length) {
    if (data == nullptr) {
        return (0);
    }

    if (length == 0) {
        length = strlen(data);
    }

    size_t written = 0;
#ifdef ENABLE_JTAG_CONFIG_INTERFACE
    while (written < length) {
        size_t to_write = (length - written > TX_BUFFER_SIZE) ? TX_BUFFER_SIZE : (length - written);
        ssize_t actual_written = (ssize_t)usb_serial_jtag_write_bytes(&data[written], to_write, pdMS_TO_TICKS(1000));
        if (actual_written <= 0) {
            break;
        }
        written += actual_written;
    }
#else
    while (written < length) {
        size_t to_write = (length - written > TX_BUFFER_SIZE) ? TX_BUFFER_SIZE : (length - written);
        ssize_t actual_written = (ssize_t)uart_write_bytes(UART_NUM_0, &data[written], to_write);
        if (actual_written <= 0) {
            break;
        }
        written += actual_written;
    }
#endif
    return (written);
}

void ConfigInterface::handle_wifi_setup(ConfigInterface* instance, int mode, const char* data, size_t length) {
    if (instance == nullptr) {
        return;
    }
    App* app = instance->app;
    SysConfig* cfg = app->get_config();
    if (cfg == nullptr) {
        return;
    }

    char ssid[32]{ 0 };
    char pwd[64]{ 0 };
    ConfigInterface::extract_link_pwd(data, length, TTY_KEY_WIFI_SETUP, ssid, sizeof (ssid), nullptr, 0, pwd, sizeof (pwd));

    cfg->set_ssid(ssid);
    cfg->set_password(pwd);
#ifdef DISPLAY_STATE        
    cfg->print_parms("Config response");
#endif        

    DisplayI2C* display = app->get_display();
    if (display != nullptr) {
        app->set_display_page(DisplayPage::menu);
        display->clear();
        display->print(0, 0, "WiFi-setup:");
        display->print(0, 1, ssid);
        display->print(0, 2, pwd);
        display->print(0, 3, "rebooting in 3s");
        display->update();
    }

    app->request_sys_config_update();
    vTaskDelay(pdMS_TO_TICKS(3000));
    esp_event_post(APP_EVENT, (int32_t)AppEvent::reboot, nullptr, 0, pdMS_TO_TICKS(1));
}

void ConfigInterface::handle_id_response(ConfigInterface* instance, int mode, const char* data, size_t length) {
    const char* ip_addr = nullptr;
    SensorDriver* driver = nullptr;
    App* app = instance->app;
    if (app != nullptr) {
        if (app->get_station() != nullptr) {
            ip_addr = app->get_station()->get_ip();
        }
        if (app->get_sensor() != nullptr) {
            driver = app->get_sensor()->get_driver();
        }
    }

    char* device_id_json = Tools::get_device_id_json(ip_addr, driver, app->get_display());
    send(device_id_json, strlen(device_id_json));
    free(device_id_json);
}

void ConfigInterface::handle_sensor_response(ConfigInterface* instance, int mode, const char* data, size_t length) {
    size_t len = 0;
    char *json_response = instance->app->get_sensor()->get_json(len);
    send(json_response, len);
    free(json_response);
}

void ConfigInterface::handle_website_output(ConfigInterface* instance, int mode, const char* data, size_t length) {
    const char* website = WebServer::webserver_resp_str_1;
    size_t len = strlen(website);
    send(website, len);
}

void ConfigInterface::handle_restart(ConfigInterface* instance, int mode, const char* data, size_t length) {
    char* reboot_json = Tools::get_reboot_json(); 
    send(reboot_json, strlen(reboot_json));
    free(reboot_json);

    AppEvent message = (mode == 9) ? AppEvent::factory_reset : AppEvent::reboot;
    esp_event_post(APP_EVENT, (int32_t)message, nullptr, 0, pdMS_TO_TICKS(1));
}
        
void ConfigInterface::handle_config_response(ConfigInterface* instance, int mode, const char* data, size_t length) {
    App* app = instance->app;
    SysConfig* cfg = app->get_config();
    if (cfg != nullptr) {
        char* p = strstr(data, "/config=");
        if (p != nullptr) {
            char* buffer = (char*)malloc(length + 8);
            if (buffer != nullptr) {
                memset(buffer, 0, length + 8);
                strncpy(buffer, data, length + 1);
                cfg->import_json(buffer, length);
                esp_event_post(APP_EVENT, (int32_t)AppEvent::nvm_update, nullptr, 0, pdMS_TO_TICKS(1));
                free(buffer);
            }
        } else {
            char* str_json = cfg->get_json(false, true);
            if (str_json != nullptr) {
                send(str_json, strlen(str_json));
                free(str_json);
            }
        }
    }
}

void ConfigInterface::process_command(const char* data, size_t length) {
#ifdef DISPLAY_STATE        
    ESP_LOGI(TAG, "ConfigInterface::process_command(\"%s\", %zu)", data, length);
#endif
    app->reload_screensaver();
    for (size_t i = 0; i < SIZEOFARRAY(function_tab); i++) {
        if (strncmp(data, function_tab[i].key, strlen(function_tab[i].key)) == 0) {
            (*function_tab[i].callback)(this, function_tab[i].mode, data, length);
            break;
        }
    }
}

void ConfigInterface::handle_mqtt_broker(ConfigInterface* instance, int mode, const char* data, size_t length) {
    if (instance == nullptr) {
        return;
    }
    App* app = instance->app;
    SysConfig* cfg = app->get_config();
    if (cfg == nullptr) {
        return;
    }

    char broker[64]{ 0 };
    char username[32]{ 0 };
    char pwd[64]{ 0 };
    ConfigInterface::extract_link_pwd(data, length, TTY_KEY_MQTT_BROKER,
        broker, sizeof (broker), username, sizeof (username), pwd, sizeof (pwd));

    cfg->set_mqtt_broker(broker);
    cfg->set_mqtt_username(username);
    cfg->set_mqtt_password(pwd);

    esp_event_post(APP_EVENT, (int32_t)AppEvent::mqtt_configure, nullptr, 0, pdMS_TO_TICKS(1));
}

void ConfigInterface::extract_link_pwd(const char* _data, size_t _length, const char* _key,
    char* _link, size_t _len_link, char* _username, size_t _len_username, char* _password, size_t _len_password) {

    char buffer[256]{ 0 };
    _length = MIN(sizeof (buffer) - 1, _length);
    memcpy(buffer, _data, _length);
    buffer[_length] = '\0';

    int i = strlen(_key);
    if (buffer[i] == '=') {
        char* p1 = &buffer[i + 1];
        char* p2 = strstr(p1, ":");
        if (p2 != nullptr) {
            *p2++ = 0;

            char* user = nullptr;
            char* pwd  = nullptr;

            char* p3 = strstr(p2, ":");
            if (p3 == nullptr) {
                pwd = p2;
            } else {
                *p3++ = '\0';
                user = p2;
                pwd  = p3;
            }           

            if ((user != nullptr) && (_username != nullptr) && (_len_username > 1)) {
                memset(_username, 0, _len_username);
                strncpy(_username, user, _len_username - 1);
            }

            if ((pwd != nullptr) && (_password != nullptr) && (_len_password > 1)) {
                memset(_password, 0, _len_password);
                strncpy(_password, pwd, _len_password - 1);
            }

        }

        if ((_link != nullptr) && (_len_link > 1)) {
            memset(_link, 0, _len_link);
            strncpy(_link, p1, _len_link - 1);
        }
    }
}

void ConfigInterface::handle_par(ConfigInterface* _instance, int _mode, const char* _data, size_t _length) {
    App* app = _instance->app;
    SysConfig* cfg = app->get_config();
    if (cfg == nullptr) {
        return;
    }

    char key[32]{ 0 };
    char value[32]{ 0 };

    char* p = strstr(_data, TTY_KEY_PAR);
    if (p == nullptr) {
        return;
    }

    p = &p[strlen(TTY_KEY_PAR)];
    if (*p != '=') {
        return;
    }
    p++;
    int i;
    for (i = 0; (i < (sizeof (key) - 1)) && ((&p[i] - _data) < _length) && (p[i] != ':'); i++) {
        key[i] = p[i];
    }
    strncpy(value, &p[i + 1], sizeof(value) - 1);

    const char* format = "{\n\"%s\": \"%s\"\n}\n";
    size_t size = snprintf(nullptr, 0, format, key, value) + 8;
    char* json_string = (char*)malloc(size);
    memset(json_string, 0, size);
    snprintf(json_string, size, format, key, value);

    cfg->import_json(json_string, size);

    free(json_string);
}

void ConfigInterface::handle_test(ConfigInterface* _instance, int _mode, const char* _data, size_t _length) {
    printf("Testing is currently disabled.\n");
}
