makreck/Rase/firmware/esp32/src/display_i2c_oled128x64.cpp

/*
 * ==============================================================================
 *
 *  PROJECT:     "Rase" Radio Sensor Project,    ESP32-S3 Station Device Firmware
 *  COPYRIGHT:   (C)2025-2026 KKS-Elektronik,  M. Kreck, <makreck@googlemail.com>
 *
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
 * ==============================================================================
 */

#include "app.hpp"

// #define DISPLAY_STATE

#define SSD_CMD_SET_COLUMN_LOW          (0x00)
#define SSD_CMD_SET_COLUMN_HIGH         (0x10)
#define SSD_CMD_SET_MEMORY_ADDR_MODE    (0x20)
#define SSD_CMD_SET_COLUMN_RANGE        (0x21)
#define SSD_CMD_SET_PAGE_RANGE          (0x22)
#define SSD_CMD_SET_START_LINE          (0x40)
#define SSD_CMD_SET_DISPLAY_CLOCK_EN    (0x80)
#define SSD_CMD_SET_CONTRAST            (0x81)
#define SSD_CMD_SET_DC_DC_ENABLE        (0x8d)
#define SSD_CMD_SET_SEGMENT_REMAP       (0xa1) // 0 ... 127
#define SSD_CMD_OUTPUT_FOLLOWS_RAM      (0xa4)
#define SSD_CMD_OUTPUT_IGNORES_RAM      (0xa5)
#define SSD_CMD_NORMAL_DISPLAY          (0xa6)
#define SSD_CMD_INVERT_DISPLAY          (0xa7)
#define SSD_CMD_SET_MULTIPLEX           (0xa8)
#define SSD_CMD_DISPLAY_OFF             (0xae)
#define SSD_CMD_DISPLAY_ON              (0xaf)
#define SSD_CMD_SET_PAGE_START_ADDRESS  (0xb0) // 0xb0 ... 0xb7
#define SSD_CMD_SET_COM_SCAN_DEC        (0xc0)
#define SSD_CMD_SET_COM_SCAN_INC        (0xc8)
#define SSD_CMD_SET_DISPLAY_OFFSET      (0xd3)
#define SSD_CMD_SET_DISPLAY_CLOCK       (0xd5)
#define SSD_CMD_SET_PRECHARGE_PERIOD    (0xd9)
#define SSD_CMD_SET_COM_PIN_CONFIG      (0xda)
#define SSD_CMD_SET_VCOM_DESELECT       (0xdb)
#define SSD_CMD_SET_DIVIDE_RATIO        (0xf0)

#define SSD_PAR_SEQUENTIAL_COM_PIN      (0x12)
#define SSD_PAR_CONTRAST_VALUE          (0xFF) // 0xCF vs. 0xDF vs. 0xFF
#define SSD_PAR_MULTIPLEX_DUTY_CYCLE    (0x3F) // 1/64 duty cycle
#define SSD_PAR_PRECHARGED_PERIOD_TIME  (0x22) // (0xF1)
#define SSD_PAR_VCOMH_DESELECT_LEVEL    (0x20) // (0x40)
#define SSD_PAR_DISPLAY_OFFSET          (0x00) // no offset
#define SSD_PAR_DC_DC_ENABLE            (0x14) // DC-DC enable
#define SSD_PAR_DC_DC_DISABLE           (0x10) // DC-DC disable
#define SSD_PAR_CLOCK_DIVIDE_RATIO      (0xF0) // Display clock divide ratio
#define SSD_PAR_ADRMODE_HORZ            (0x00) // Page addressing mode: horizontal
#define SSD_PAR_ADRMODE_VERT            (0x01) // Page addressing mode: vertical
#define SSD_PAR_ADRMODE_PAGE            (0x10) // Page addressing mode: pages
#define SSD_PAR_ADRMODE_INV             (0x11) // Page addressing mode: invalid
#define SSD_PAR_COLUMN_START            (0x00) // Start column is 0
#define SSD_PAR_COLUMN_END_SSD1306      (0x7F) // Last column on SSD1306 is 127
#define SSD_PAR_COLUMN_END_SSD1106      (0x83) // Last column on SSD1106 is 131


const char DisplayOLED128x64::ssd1306_init_sequence[] = {
    SSD_CMD_DISPLAY_OFF,               // display off

    SSD_CMD_SET_MEMORY_ADDR_MODE,      // set memory addressing mode	
	SSD_PAR_ADRMODE_PAGE,              // 0x00 = horizontal addressing mode, 0x01 = vertical addressing mode, 0x10 = page addressing mode (reset), 0x11 = invalid

	SSD_CMD_SET_PAGE_START_ADDRESS,    // set page start address for page addressing mode, +0 to +7
	
    SSD_CMD_SET_COM_SCAN_INC,          // set COM output scan direction
	
    SSD_CMD_SET_COLUMN_LOW,            // set low column address
	SSD_CMD_SET_COLUMN_HIGH,           // set high column address
	SSD_CMD_SET_START_LINE,            // set start line address
	
    SSD_CMD_SET_CONTRAST,              // set contrast control register
	SSD_PAR_CONTRAST_VALUE,            // contrast value 0x00 ... 0xFF	

    SSD_CMD_SET_SEGMENT_REMAP,         // set segment re-map 0 to 127

    SSD_CMD_NORMAL_DISPLAY,            // set normal display

    SSD_CMD_SET_MULTIPLEX,             // set multiplex ratio
	SSD_PAR_MULTIPLEX_DUTY_CYCLE,      // multiplex ratio (duty cycle) 1 to 64

    SSD_CMD_OUTPUT_FOLLOWS_RAM,        // 0xA4 = output follows RAM content, 0xa5 = output ignores RAM content

    SSD_CMD_SET_DISPLAY_OFFSET,        // set display offset
	SSD_PAR_DISPLAY_OFFSET,            // no offset

    // SSD_CMD_SET_COLUMN_RANGE,          // set column range, SSD1306 = 0 ... 127, SSD1106 = 0 ... 131
    // SSD_PAR_COLUMN_START,              // First column is always 0
    // SSD_PAR_COLUMN_END_SSD1306,        // Last column on SSD1306 is 127

    SSD_CMD_SET_DISPLAY_CLOCK,         // set display clock divide ratio/oscillator frequency
	SSD_PAR_CLOCK_DIVIDE_RATIO,        // clock divide ratio

	SSD_CMD_SET_PRECHARGE_PERIOD,      // set pre-charge period
	SSD_PAR_PRECHARGED_PERIOD_TIME,    // period time

	SSD_CMD_SET_COM_PIN_CONFIG,        // set com pins hardware configuration
	SSD_PAR_SEQUENTIAL_COM_PIN,        //
	
    SSD_CMD_SET_VCOM_DESELECT,         // set Vcom H
	SSD_PAR_VCOMH_DESELECT_LEVEL,      // 0x20 = 0.77 x Vcc

	SSD_CMD_SET_DC_DC_ENABLE,          // set DC-DC enable
	SSD_PAR_DC_DC_ENABLE,              // DC-DC enable part #2 (enable = 0x14, disable = 0x10)

	SSD_CMD_DISPLAY_ON,                // turn on OLED panel 
};

esp_err_t DisplayOLED128x64::init(void) {
    for (int i = 0; i < sizeof (ssd1306_init_sequence); i++) {
        send_command(ssd1306_init_sequence[i]);
    }
    return (ESP_OK);
}

esp_err_t DisplayOLED128x64::clear(void) {
    memset(displayBuffer.s, 0, sizeof (displayBuffer.s));
    return (ESP_OK);
}

esp_err_t DisplayOLED128x64::setLogo(void) {
    if (swap_vertical) {
        int n = 1023;
        for (int i = 0; i < 1024; i++, n--) {
            displayBuffer.s[(i + 256) & 0x3ff] = bitReverseTab[kks_logo_image[n & 0x3ff]];
        }
        print(0, 3, "   Powered by   ", 16);
    } else {
        memcpy(displayBuffer.s, kks_logo_image, sizeof (displayBuffer.s));
        print(0, 0, "   Powered by   ", 16);
    }
    return (ESP_OK);
}

esp_err_t DisplayOLED128x64::cursor_pos(int row, int col) {
    return (ESP_OK);
}

esp_err_t DisplayOLED128x64::update(void) {
#ifdef DISPLAY_STATE
    ESP_LOGI(TAG, "DisplayOLED128x64::update()");
#endif

    int i = 0;

    for (uint8_t y = 0; y < 8; y++) {
        send_command(SSD_CMD_SET_PAGE_START_ADDRESS + y);
        send_command(scan_start[0]);
        send_command(scan_start[1]);

        for (uint8_t x = 0; x < 128; x++) {
            send_data(displayBuffer.s[i++]);
        }

        for (uint8_t x = 128; x < pixels_x; x++) {
            send_data(0x00);
        }
    }

#ifdef DISPLAY_STATE
    ESP_LOGI(TAG, "DisplayOLED128x64::update() -> Done.");
#endif
    return (ESP_OK);
}

esp_err_t DisplayOLED128x64::send_command(uint8_t cmd) {
    i2c_buffer[0] = 0x00;
    i2c_buffer[1] = cmd;
    return (i2c_master_write_to_device(port, slave_address, i2c_buffer, 2, pdMS_TO_TICKS(LCD_IO_TIMEOUT_MS)));
}

esp_err_t DisplayOLED128x64::send_data(uint8_t data) {
    i2c_buffer[0] = 0x40;
    i2c_buffer[1] = data;
    return (i2c_master_write_to_device(port, slave_address, i2c_buffer, 2, pdMS_TO_TICKS(LCD_IO_TIMEOUT_MS)));
}

esp_err_t DisplayOLED128x64::print_large(int x, int y, const char* text, size_t length) {
    if (length == 0) {
        length = strlen(text);
    }
    for (int n = 0; n < (int)length; n++) {
        render_large_glyph(x + n * 2, y, text[n]);
    }
    return (ESP_OK);
}

esp_err_t DisplayOLED128x64::print(int x, int y, const char* text, size_t length) {
    if (length == 0) {
        length = strlen(text);
    }
    for (int n = 0; n < (int)length; n++) {
        render_glyph(x + n, y, text[n]);
    }
    return (ESP_OK);
}

esp_err_t DisplayOLED128x64::set_pixel(int x, int y, bool state) {
    if ((x < 0) || (x >= 128) || (y < 0) || (y >= 64)) {
        return (ESP_FAIL);
    }
    if (state) {
        displayBuffer.a[y / 8][x] |= (uint8_t)(1 << (y % 8));
    } else {
        displayBuffer.a[y / 8][x] &= (uint8_t)(0xff ^ (1 << (y % 8)));
    }
    return (ESP_OK);
}

esp_err_t DisplayOLED128x64::invert_row(int row) {
    int y = row * 2;
    if (swap_vertical) {
        y = (7 - y) ^ 0x01;
    }
    y &= 0x07;
    for (int x = 0; x < 128; x++) {
        displayBuffer.a[y + 0][x] ^= 0xff;
        displayBuffer.a[y + 1][x] ^= 0xff;
    }
    return (ESP_FAIL);
}

uint32_t DisplayOLED128x64::font_byte_16_to_32_bit(uint16_t fontWord) {
    uint32_t fontWord32 = 0;
    for (int i = 0; i < 16; i++) {
        if (fontWord & (1 << i)) {
            fontWord32 |= (uint32_t)(3 << (i * 2));
        }
    }
    return (fontWord32);
}

uint8_t DisplayOLED128x64::check_bit_swap(uint8_t fontData) {
    if (swap_vertical) {
        fontData = (bitReverseTab[(unsigned int)fontData]);
    }
    return (fontData);
}

uint16_t DisplayOLED128x64::check_bit_swap(uint16_t fontData) {
    if (swap_vertical) {
        uint8_t lsb = ((fontData >> 0) & 0xff);
        uint8_t msb = ((fontData >> 8) & 0xff);
        fontData = (bitReverseTab[(unsigned int)lsb] << 8) | (bitReverseTab[(unsigned int)msb]);
    }
    return (fontData);
}

int DisplayOLED128x64::check_line_swap8(int line) {
    if (swap_vertical) {
        line = (7 - line) ^ 0x01;
    }
    return (line & 0x07);
}

int DisplayOLED128x64::check_line_swap16(int line) {
    if (swap_vertical) {
        line = (7 - line) ^ 0x01;
    }
    return (line);
}

int DisplayOLED128x64::checkColumnSwap(int column) {
    if (swap_vertical) {
        column = 127 - column;
    }
    return (column & 0x7f);
}

esp_err_t DisplayOLED128x64::render_glyph(int x, int y, char glyphCode) {
    if ((x < 0) || (x >= 16) || (y < 0) || (y >= 8)) {
        return (ESP_FAIL);
    }

    TypeConvert tc{ 0 };

    const uint16_t* p = &font8x16_basic[(int)(glyphCode & 0x7f)][0];
    int col = x * 8;
    for (int n = 0; n < 8; n++) {
        tc.w[0] = check_bit_swap(p[n]);
        displayBuffer.a[check_line_swap8(y * 2 + 0)][checkColumnSwap(col + n)] = tc.b[0]; 
        displayBuffer.a[check_line_swap8(y * 2 + 1)][checkColumnSwap(col + n)] = tc.b[1]; 
    }

    return (ESP_OK);
}

esp_err_t DisplayOLED128x64::render_large_glyph(int x, int y, char glyphCode) {
    if ((x < 0) || (x >= 15) || (y < 0) || (y >= 7)) {
        return (ESP_FAIL);
    }
    
    TypeConvert tc{ 0 };

    const uint16_t* p = &font8x16_basic[(int)(glyphCode & 0x7f)][0];
    int col = x * 8;
    for (int n = 0; n < 8; n++) {
        tc.dw = font_byte_16_to_32_bit(check_bit_swap(p[n]));
        int i = n * 2;

        if (swap_vertical) {
            displayBuffer.a[check_line_swap16(y * 2 + 2)][checkColumnSwap(col + i)] = tc.b[0];
            displayBuffer.a[check_line_swap16(y * 2 + 2)][checkColumnSwap(col + i + 1)] = tc.b[0];

            displayBuffer.a[check_line_swap16(y * 2 + 3)][checkColumnSwap(col + i)] = tc.b[1];
            displayBuffer.a[check_line_swap16(y * 2 + 3)][checkColumnSwap(col + i + 1)] = tc.b[1];

            displayBuffer.a[check_line_swap16(y * 2 + 0)][checkColumnSwap(col + i)] = tc.b[2];
            displayBuffer.a[check_line_swap16(y * 2 + 0)][checkColumnSwap(col + i + 1)] = tc.b[2];

            displayBuffer.a[check_line_swap16(y * 2 + 1)][checkColumnSwap(col + i)] = tc.b[3];
            displayBuffer.a[check_line_swap16(y * 2 + 1)][checkColumnSwap(col + i + 1)] = tc.b[3];
        } else {
            displayBuffer.a[check_line_swap16(y * 2 + 0)][checkColumnSwap(col + i)] = tc.b[0];
            displayBuffer.a[check_line_swap16(y * 2 + 0)][checkColumnSwap(col + i + 1)] = tc.b[0];

            displayBuffer.a[check_line_swap16(y * 2 + 1)][checkColumnSwap(col + i)] = tc.b[1];
            displayBuffer.a[check_line_swap16(y * 2 + 1)][checkColumnSwap(col + i + 1)] = tc.b[1];

            displayBuffer.a[check_line_swap16(y * 2 + 2)][checkColumnSwap(col + i)] = tc.b[2];
            displayBuffer.a[check_line_swap16(y * 2 + 2)][checkColumnSwap(col + i + 1)] = tc.b[2];

            displayBuffer.a[check_line_swap16(y * 2 + 3)][checkColumnSwap(col + i)] = tc.b[3];
            displayBuffer.a[check_line_swap16(y * 2 + 3)][checkColumnSwap(col + i + 1)] = tc.b[3];
        }
    }

    return (ESP_OK);
}

esp_err_t DisplayOLED128x64::set_rotation(int _degree) {
    swap_vertical = (_degree == 180);
    return (ESP_OK);
}

esp_err_t DisplayOLED128x64::set_contrast(float value) {
    uint8_t data = (uint8_t)(MAX(0.0f, MIN(1.0f, value)) * 255.0f);
    send_command(SSD_CMD_SET_CONTRAST);
    send_command(data);
    return (ESP_OK);
}

esp_err_t DisplayOLED128x64::off(void) {
    ESP_LOGI(TAG, "DisplayOLED128x64::off()");
    send_command(SSD_CMD_DISPLAY_OFF);
    return (ESP_OK);
}

esp_err_t DisplayOLED128x64::on(void) {
    ESP_LOGI(TAG, "DisplayOLED128x64::on()");
    send_command(SSD_CMD_DISPLAY_ON);
    return (ESP_OK);
}

esp_err_t DisplayOLED128x64::detect_controller(void) {
    send_command(SSD_CMD_DISPLAY_OFF);
    vTaskDelay(pdMS_TO_TICKS(50));
    
    uint8_t out = 0x00;
    uint8_t in = 0x00;
    i2c_master_write_read_device(port, slave_address, &out, 1, &in, 1, pdMS_TO_TICKS(LCD_IO_TIMEOUT_MS));

    controller = (OLEDController)(in & 0x0f);

    switch (controller) {
        case OLEDController::SSD1306_0_96_inch_128x64: {
            controller_type = "0.96'' SSD1306 128 x 64";
            pixels_x = 128;
            pixels_y = 64;
            scan_start[0] = 0x00;
            scan_start[1] = 0x10;
        } break;

        case OLEDController::SSD1306_0_91_inch_128x64_yb: {
            controller_type = "0.91'' SSD1306 128 x 64 (yellow/blue)";
            pixels_x = 128;
            pixels_y = 64;
            scan_start[0] = 0x00;
            scan_start[1] = 0x10;
        } break;

        case OLEDController::SSD1306_0_91_inch_128x64: {
            controller_type = "0.91'' SSD1306 128 x 64 (white/yellow/blue)";
            pixels_x = 128;
            pixels_y = 64;
            scan_start[0] = 0x00;
            scan_start[1] = 0x10;
        } break;

        case OLEDController::SH1106_1_3_inch_132x64_white: {
            controller_type = "1.3'' SH1106 132 x 64 (white)";
            pixels_x = 132;
            pixels_y = 64;
            scan_start[0] = 0x02;
            scan_start[1] = 0x10;
        } break;

        case OLEDController::SH1106_1_3_inch_132x64_blue: {
            controller_type = "1.3'' SH1106 132 x 64 (blue)";
            pixels_x = 132;
            pixels_y = 64;
            scan_start[0] = 0x02;
            scan_start[1] = 0x10;
        } break;

        default: {
            controller_type = "unsupported";
        } break;
    }

    ESP_LOGI(TAG,
        "DisplayOLED128x64::detect_controller() = 0x%-2.2X: \"%s\" %d x %d pixels ",
        (unsigned int)in, controller_type, (int)pixels_x, (int)pixels_y);

    return (ESP_OK);
}

const char* DisplayOLED128x64::get_controller(void) {
    return (controller_type);
}
