makreck/Rase/firmware/esp32/src/display_fonts.cpp

/*
 * ==============================================================================
 *
 *  PROJECT:     "Rase" Radio Sensor Project,    ESP32-S3 Station Device Firmware
 *  COPYRIGHT:   (C)2025-2026 KKS-Elektronik,  M. Kreck, <makreck@googlemail.com>
 *
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
 * ==============================================================================
 */

#include "app.hpp"

const uint8_t bitReverseTab[256] = {
	0x00, 0x80, 0x40, 0xC0, 0x20, 0xA0, 0x60, 0xE0, 0x10, 0x90, 0x50, 0xD0, 0x30, 0xB0, 0x70, 0xF0,
	0x08, 0x88, 0x48, 0xC8, 0x28, 0xA8, 0x68, 0xE8, 0x18, 0x98, 0x58, 0xD8, 0x38, 0xB8, 0x78, 0xF8,
	0x04, 0x84, 0x44, 0xC4, 0x24, 0xA4, 0x64, 0xE4, 0x14, 0x94, 0x54, 0xD4, 0x34, 0xB4, 0x74, 0xF4,
	0x0C, 0x8C, 0x4C, 0xCC, 0x2C, 0xAC, 0x6C, 0xEC, 0x1C, 0x9C, 0x5C, 0xDC, 0x3C, 0xBC, 0x7C, 0xFC,
	0x02, 0x82, 0x42, 0xC2, 0x22, 0xA2, 0x62, 0xE2, 0x12, 0x92, 0x52, 0xD2, 0x32, 0xB2, 0x72, 0xF2,
	0x0A, 0x8A, 0x4A, 0xCA, 0x2A, 0xAA, 0x6A, 0xEA, 0x1A, 0x9A, 0x5A, 0xDA, 0x3A, 0xBA, 0x7A, 0xFA,
	0x06, 0x86, 0x46, 0xC6, 0x26, 0xA6, 0x66, 0xE6, 0x16, 0x96, 0x56, 0xD6, 0x36, 0xB6, 0x76, 0xF6,
	0x0E, 0x8E, 0x4E, 0xCE, 0x2E, 0xAE, 0x6E, 0xEE, 0x1E, 0x9E, 0x5E, 0xDE, 0x3E, 0xBE, 0x7E, 0xFE,
	0x01, 0x81, 0x41, 0xC1, 0x21, 0xA1, 0x61, 0xE1, 0x11, 0x91, 0x51, 0xD1, 0x31, 0xB1, 0x71, 0xF1,
	0x09, 0x89, 0x49, 0xC9, 0x29, 0xA9, 0x69, 0xE9, 0x19, 0x99, 0x59, 0xD9, 0x39, 0xB9, 0x79, 0xF9,
	0x05, 0x85, 0x45, 0xC5, 0x25, 0xA5, 0x65, 0xE5, 0x15, 0x95, 0x55, 0xD5, 0x35, 0xB5, 0x75, 0xF5,
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
    { 0x0000, 0x0000, 0x0000, 0x0000, 0x0000, 0x0000, 0x0000, 0x0000 }, // U+00001E (.)
    { 0x0000, 0x0000, 0x0000, 0x0000, 0x0000, 0x0000, 0x0000, 0x0000 }, // U+00001F (.)
    { 0x0000, 0x0000, 0x0000, 0x0000, 0x0000, 0x0000, 0x0000, 0x0000 }, // U+000020 ( )
    { 0x0000, 0x0000, 0x0000, 0x0000, 0x09F0, 0x0000, 0x0000, 0x0000 }, // U+000021 (!)
    { 0x0000, 0x0000, 0x00F0, 0x0030, 0x0000, 0x00F0, 0x0030, 0x0000 }, // U+000022 (")
    { 0x0000, 0x1A40, 0x07E0, 0x0258, 0x1A40, 0x07E0, 0x0258, 0x0000 }, // U+000023 (#)
    { 0x0000, 0x0000, 0x0660, 0x0490, 0x1C98, 0x0330, 0x0000, 0x0000 }, // U+000024 ($)
    { 0x0000, 0x0120, 0x0150, 0x0520, 0x0A80, 0x0480, 0x0000, 0x0000 }, // U+000025 (%)
    { 0x0000, 0x0000, 0x0600, 0x09C0, 0x0B20, 0x0C20, 0x0A20, 0x0000 }, // U+000026 (&)
    { 0x0000, 0x0000, 0x0000, 0x00F0, 0x0000, 0x0000, 0x0000, 0x0000 }, // U+000027 (')
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
};
