makreck/Rase/firmware/esp32/include/app.hpp

/*
 * ==============================================================================
 *
 *  PROJECT:     "Rase" Radio Sensor Project,    ESP32-S3 Station Device Firmware
 *  COPYRIGHT:   (C)2025-2026 KKS-Elektronik,  M. Kreck, <makreck@googlemail.com>
 *
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
 * ==============================================================================
 */

#pragma once

#include "includes.hpp"

#include "version.hpp"
#include "typedef.hpp"
#include "app_config.hpp"
#include "io_mapping.hpp"

#include "app_state.hpp"
#include "web_interface.hpp"
#include "tools.hpp"
#include "events.hpp"
#include "color.hpp"
#include "sw_i2c_hal.hpp"
#include "display_i2c.hpp"
#include "button.hpp"
#include "led_controller.hpp"
#include "wifi.hpp"
#include "config_interface.hpp"
#include "driver/sensor_address.hpp"
#include "driver/sensor_driver.hpp"
#include "driver/sensor_null.hpp"
#include "driver/sensor_bm2.hpp"
#include "driver/sensor_htu21d.hpp"
#include "driver/sensor_aht21.hpp"
#include "driver/sensor_sht2.hpp"
#include "driver/sensor_sht3.hpp"
#include "driver/sensor_hdc1080.hpp"
#include "channel_history.hpp"
#include "sensor_node.hpp"
#include "sensor_device.hpp"
#include "sd_card.hpp"
#include "web_server.hpp"
#include "mqtt.hpp"
#include "sys_config.hpp"
#include "config_interface.hpp"
#include "app_menu.hpp"

#define TASK_DEFAULT_PRIORITY   (20)
#define TASK_SMALL_STACKSIZE    (1024)
#define TASK_DEFAULT_STACKSIZE  (4096)
#define TASK_EXTENDED_STACKSIZE (8192)
#define TASK_WATCHDOG_TIMEOUT   (90000)

#define POWER_UP_DELAY_US       (100000)
#define POWER_UP_DELAY_MS       (100)
#define POWER_MCU_FREQ_MIN_MHZ  (80)
#define POWER_MCU_FREQ_MAX_MHZ  (240)

#define APP_DRV_LIST_MAX        (16)

enum class DisplayPage {
    invalid      = 0,
    title_screen = 1,
    menu         = 2,    
    value_page   = 3,
};

extern const char* str_display_layout[3];

class App {
    private:

        struct {
            bool             exitApp          = false;
            TaskHandle_t     task_handle       = nullptr;
            
            SysConfig*       cfg              = nullptr;
            LEDController*   led              = nullptr;
            Button*          button           = nullptr;
            DisplayI2C*      display          = nullptr;
            Wifi_Station*    station          = nullptr;
            WebServer*       webserver        = nullptr;
            Mqtt*            mqtt             = nullptr;
            SensorDriver*    driver           = nullptr;
            SensorDevice*    sensor           = nullptr;
            SDCard*          sdc              = nullptr;
            ConfigInterface* cmd              = nullptr;
            
            SensorReading    reading;
            ButtonState      btnState;

            const MenuItem*  menu             = nullptr;
            size_t           menu_count       = 0;
            int32_t          menuSelect       = 1;
            int32_t          menuStart        = 1;
            MenuItem         dynamicMenu[16]{ 0, nullptr };
            char             dynamicMenuString[256]{ 0 };

            int32_t          display_request  = 0;
            int32_t          display_update   = 0;
            DisplayPage      display_page     = DisplayPage::invalid;

            uint32_t         display_off_time = 0;
            uint64_t         update_thr_time  = 0;

            union {
                uint32_t f = 0;
                struct {
                    uint32_t error            : 1;
                    uint32_t display_off      : 1;
                    uint32_t display_lock     : 1;

                    uint32_t reboot_req       : 1;
                    uint32_t factory_init_req : 1;
                    uint32_t nvm_update_req   : 1;
                    uint32_t display_cfg_req  : 1;
                    uint32_t driver_cfg_req   : 1;
                    uint32_t led_cfg_req      : 1;

                    uint32_t button_ready     : 1;
                    uint32_t display_ready    : 1;
                    uint32_t driver_ready     : 1;
                    uint32_t wifi_enabled     : 1;
                    uint32_t wifi_connected   : 1;
                    uint32_t website_ready    : 1;

                    uint32_t button_event     : 1;
                    uint32_t driver_query     : 1;
                    uint32_t web_api_query    : 1;
                    uint32_t website_query    : 1;
                } b;
            } flags;

            const char*      drv_scan_name[APP_DRV_LIST_MAX]{ nullptr };
            uint8_t          drv_scan_adr[APP_DRV_LIST_MAX]{0};
            SensorType       drv_scan_type[APP_DRV_LIST_MAX]{ SensorType::invalid };
        } m;

        AppState init_power(void);
        AppState init_memory(void);
        AppState init_watchdog(void);
        AppState init_config(void);
        AppState init_event_loop(void);
        AppState init_display(void);
        AppState init_LEDs(void);
        AppState init_buttons(void);
        AppState init_wifi(void);
        AppState init_webserver(void);
        AppState init_driver(void);
        AppState init_mqtt(void);
        AppState init_sdcard(void);

        AppState print_net_Info(void);
        AppState print_measuring_info(uint8_t mode = 0);
        AppState print_large_text(int start);
        AppState print_Menu(void);

        void     display_next(void);
        void     flip_display(void);
        bool     reload_display_timeout(void);
        void     set_display_contrast(float value);
        void     set_Menu(const MenuItem* items, const size_t count);
        void     reset_Menu(void);
        bool     exit_Menu(void);
        void     step_Menu(void);
        size_t   new_DynamicMenu(const char* menu_title);
        void     menu_display_short_message(int wait_ms = 1000, const char* line1 = nullptr, const char* line2 = nullptr, const char* line3 = nullptr, const char* line4 = nullptr);

        AppState select_driver(void);
        AppState switch_driver_to(uint8_t i2c_addr);
        AppState trigger_watchdog(void);

        AppState handle_nvm_update(void);
        AppState handle_LEDs(void);
        AppState handle_menu(void);
        AppState handle_display(void);
        AppState handle_config_interface(void);
        AppState handle_mqtt_client(void);
        AppState handle_config_changes(void);
        AppState handle_reboot_request(void);

        AppState check_screensaver(void);

        AppState display_value_page(void);
        AppState display_details_page(void);
        AppState display_info_page(void);

        AppState display_small_value_page(void);

        static void _app_event_handler(void* arg, esp_event_base_t event_base, int32_t event_id, void* event_data);
        esp_err_t app_event_handler(esp_event_base_t event_base, AppEvent event_id, void* event_data);

    public:
        App() {
            init();
        }
        
        ~App() {
            cleanup();
        }

        AppState init(void);
        AppState run(void);
        AppState cleanup(void);
        AppState request_sys_config_update(void);
        AppState set_display_page(DisplayPage page);
        AppState reload_screensaver(void);
        AppState lock_display(bool _locked);
        
        SysConfig*       get_config(void)    { return (m.cfg);       }
        LEDController*   get_LED(void)       { return (m.led);       }
        Button*          get_button(void)    { return (m.button);    }
        DisplayI2C*      get_display(void)   { return (m.display);   }
        Wifi_Station*    get_station(void)   { return (m.station);   }
        WebServer*       get_webserver(void) { return (m.webserver); }
        SensorDriver*    get_driver(void)    { return (m.driver);    }
        SensorDevice*    get_sensor(void)    { return (m.sensor);    }
        ConfigInterface* get_cmd(void)       { return (m.cmd);       }
};
