makreck/Rase/app/debian/include/app.h

/*
 * ==============================================================================
 *
 *  PROJECT:     "Rase" Radio Sensor Project,    Measuring and Config Application
 *  COPYRIGHT:   (C)2025-2026 KKS-Elektronik,  M. Kreck, <makreck@googlemail.com>
 *
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
 * ==============================================================================
 */

#pragma once

#if GLIB_CHECK_VERSION(2, 74, 0)
    #define APP_FLAGS (G_APPLICATION_DEFAULT_FLAGS)
#else
    #define APP_FLAGS (G_APPLICATION_FLAGS_NONE)
#endif

#define APP_WINDOW_NAME "Radio Sensor Display"

#define MAIN_WINDOW_LAYOUT "src/builder.ui.xml"

#define APP_WINDOW_MIN_WIDTH  (512)
#define APP_WINDOW_MIN_HEIGHT (384)
#define APP_WINDOW_MAX_WIDTH  (8192)
#define APP_WINDOW_MAX_HEIGHT (8192)

#define GTK_WINDOW_TITLEBAR_HEIGHT (24)

class Application {
    private:
        struct {
            int argc = 0;
            char** argv = nullptr;

            Config* cfg = nullptr;
            SensorBus* bus = nullptr;
            
            bool fTerminate = false;
            int toolIconSize = 28;

            LineRecorder* lineRecorder = nullptr;

            GError* error = nullptr;
            GtkApplication* gtkApp = nullptr;
            struct {
                GtkWidget* win            = nullptr;
                GtkWidget* baseVBox       = nullptr;
                GtkWidget*  menu_bar      = nullptr;
                GtkWidget*  toolbar       = nullptr;
                GtkWidget*  paned         = nullptr;
                GtkWidget*   frame_rec    = nullptr;
                GtkWidget*    recorder    = nullptr;
                GtkWidget*   frame_dev    = nullptr;
                GtkWidget*    devList     = nullptr;
                GtkWidget*  statusBar     = nullptr;
            
                std::vector<GtkWidget*> menu_items;
            } gtk;

            struct {
                RectEx client;
            } rc;

            pthread_t updateThread = 0;

            char status_text[1024];
            uint64_t status_timestamp = 0;
        } m;

        static gboolean _activate(GtkApplication* gtk, void* user_data);
        void activate(void);

        static gboolean _configure(GtkWindow* parentWindow, GdkEvent* event, void* user_data);
        void configure(GdkEvent* event);

        static gboolean _realize(GtkWidget* widget, void* user_data);
        void realize(GtkWidget* widget);

        static void _rowSelected(GtkListBox* self, GtkListBoxRow* row, gpointer user_data);
        void rowSelected(GtkListBoxRow* row);

        static bool _dividerCallback(void* user_param);
        bool dividerCallback(void);

        static gboolean _paned(GtkPaned* paned, GtkScrollType* scroll_type, gpointer user_data);
        bool paned(GtkPaned* paned, GtkScrollType* scroll_type);

        static gboolean _idle_update_task(gpointer object);
        void idle_update_task(void);

        static gboolean _busUpdate(gpointer object);
        void busUpdate(void);

        static gboolean _statusUpdate(gpointer object);
        void statusUpdate(void);
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
